uw-x/tinysdr/hardware/pcb-tinysdr/XSDR_FPGA_back.kicad_sch

## KiCad design hardware/pcb-tinysdr/XSDR_FPGA_back.kicad_sch (2022-02-07)

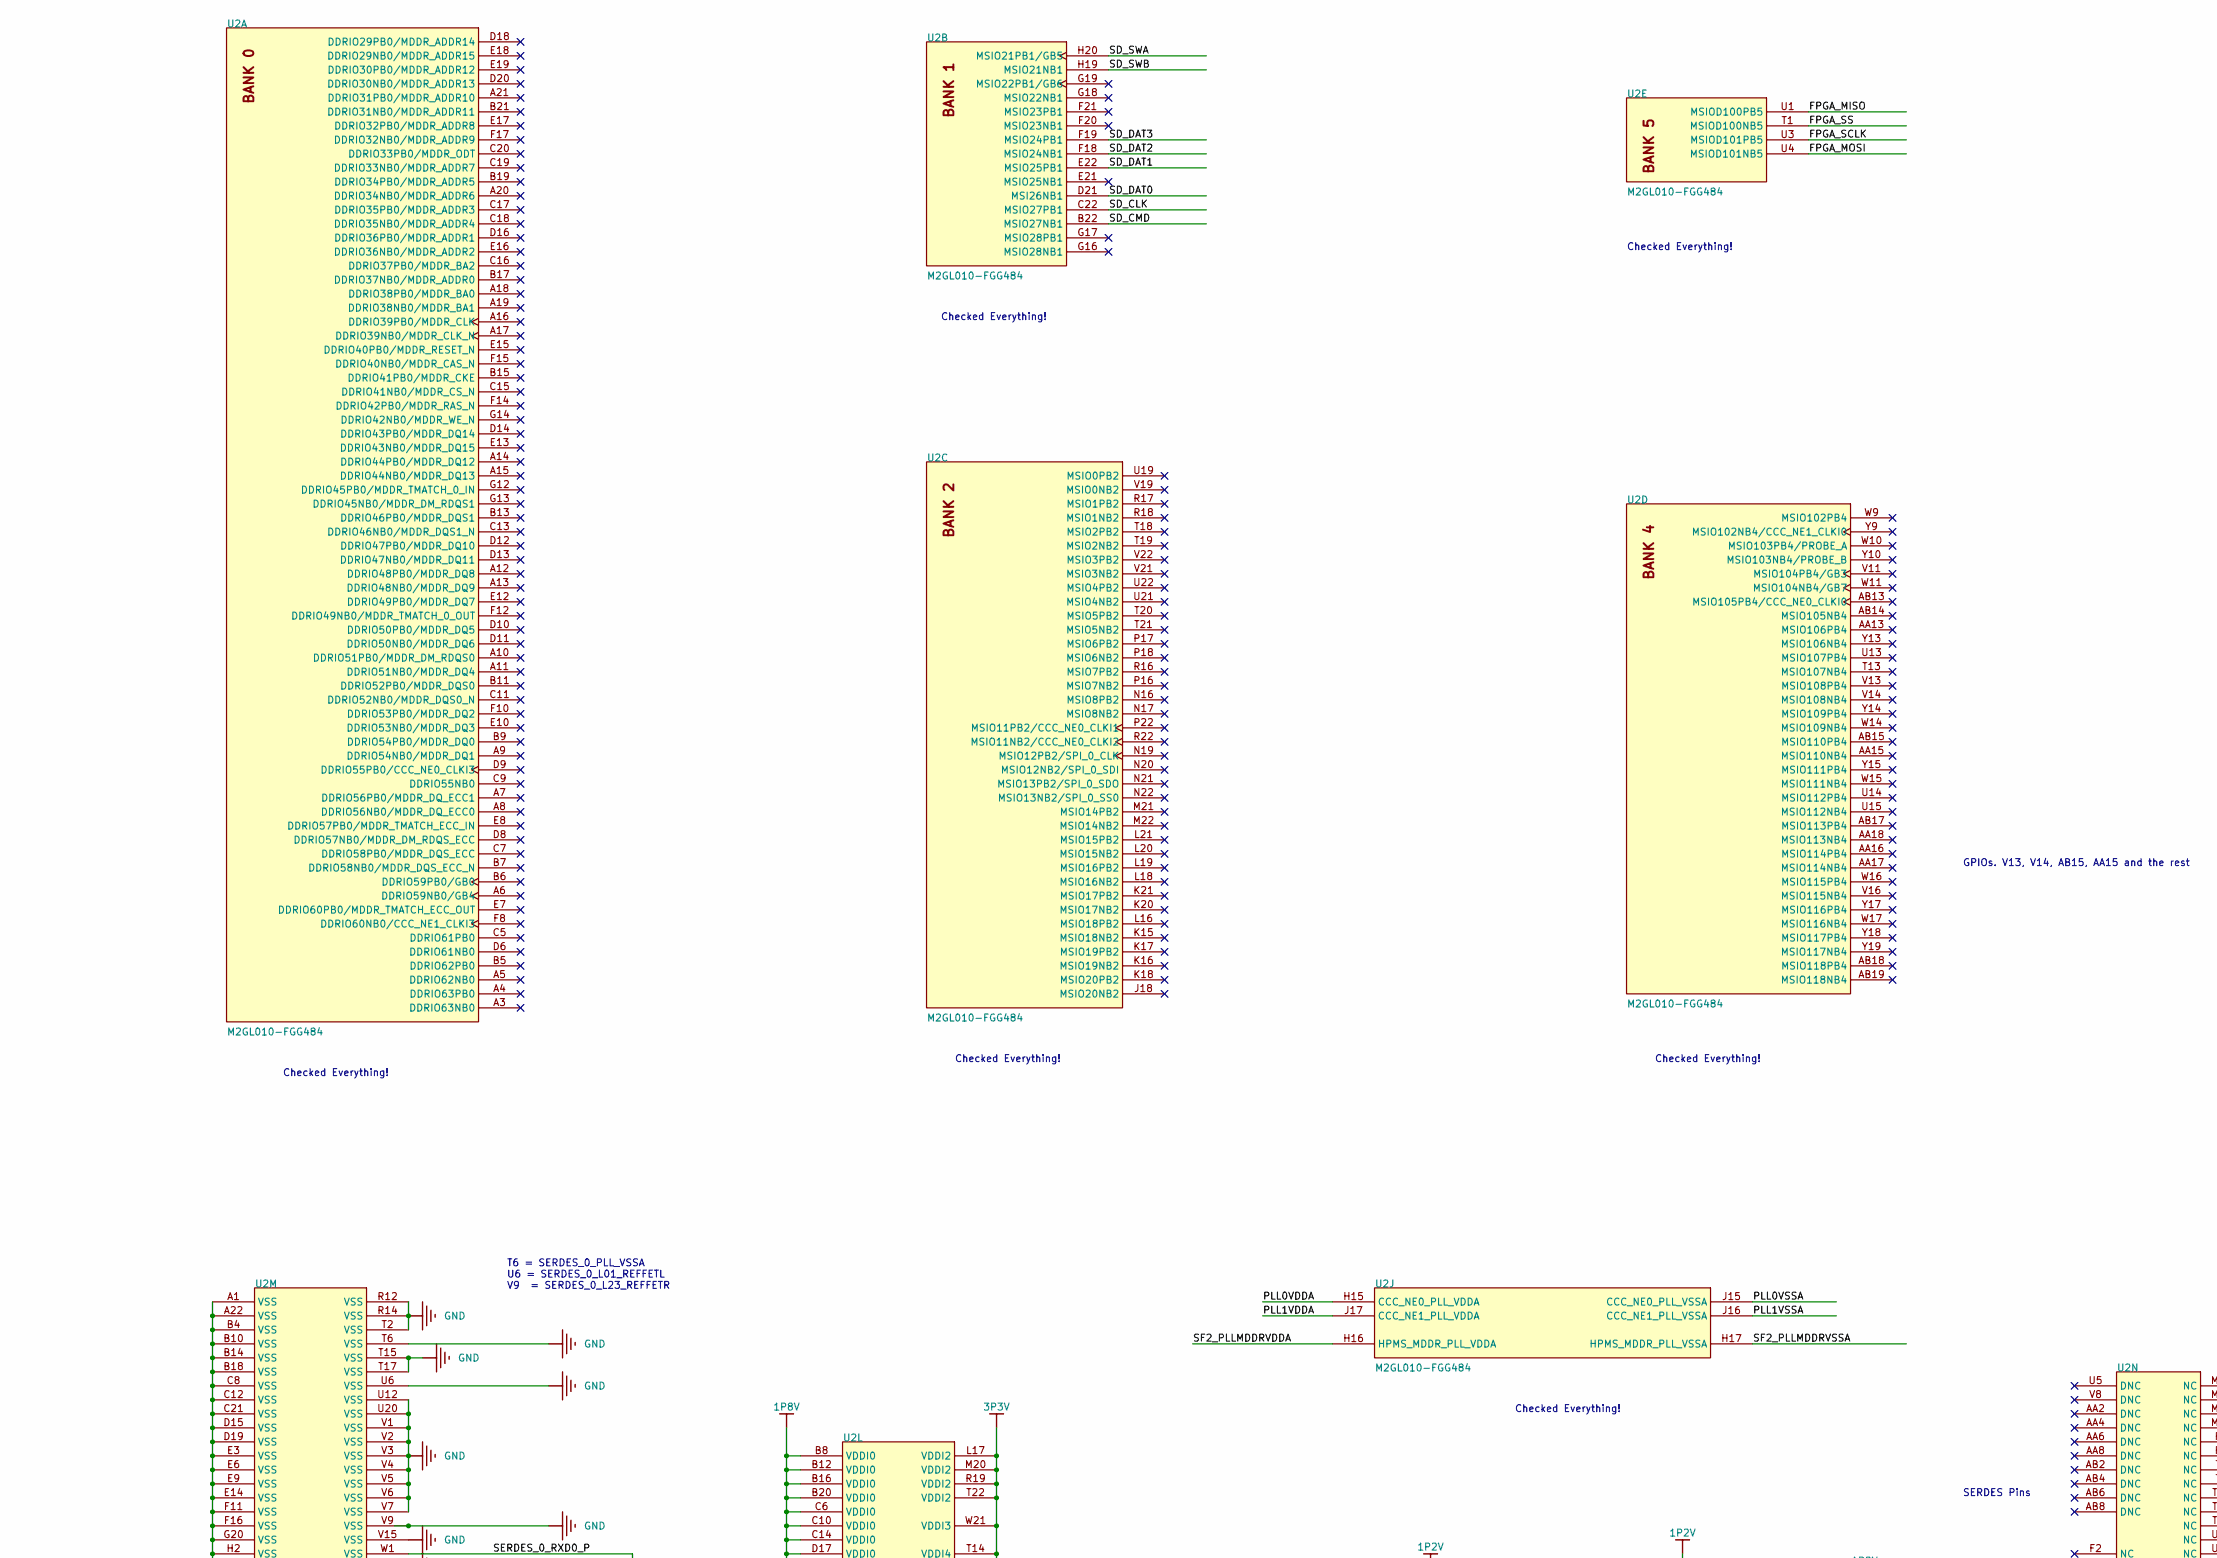
[picture p29: schematic XSDR_FPGA_back.kicad_sch, part in row 1, column 1]

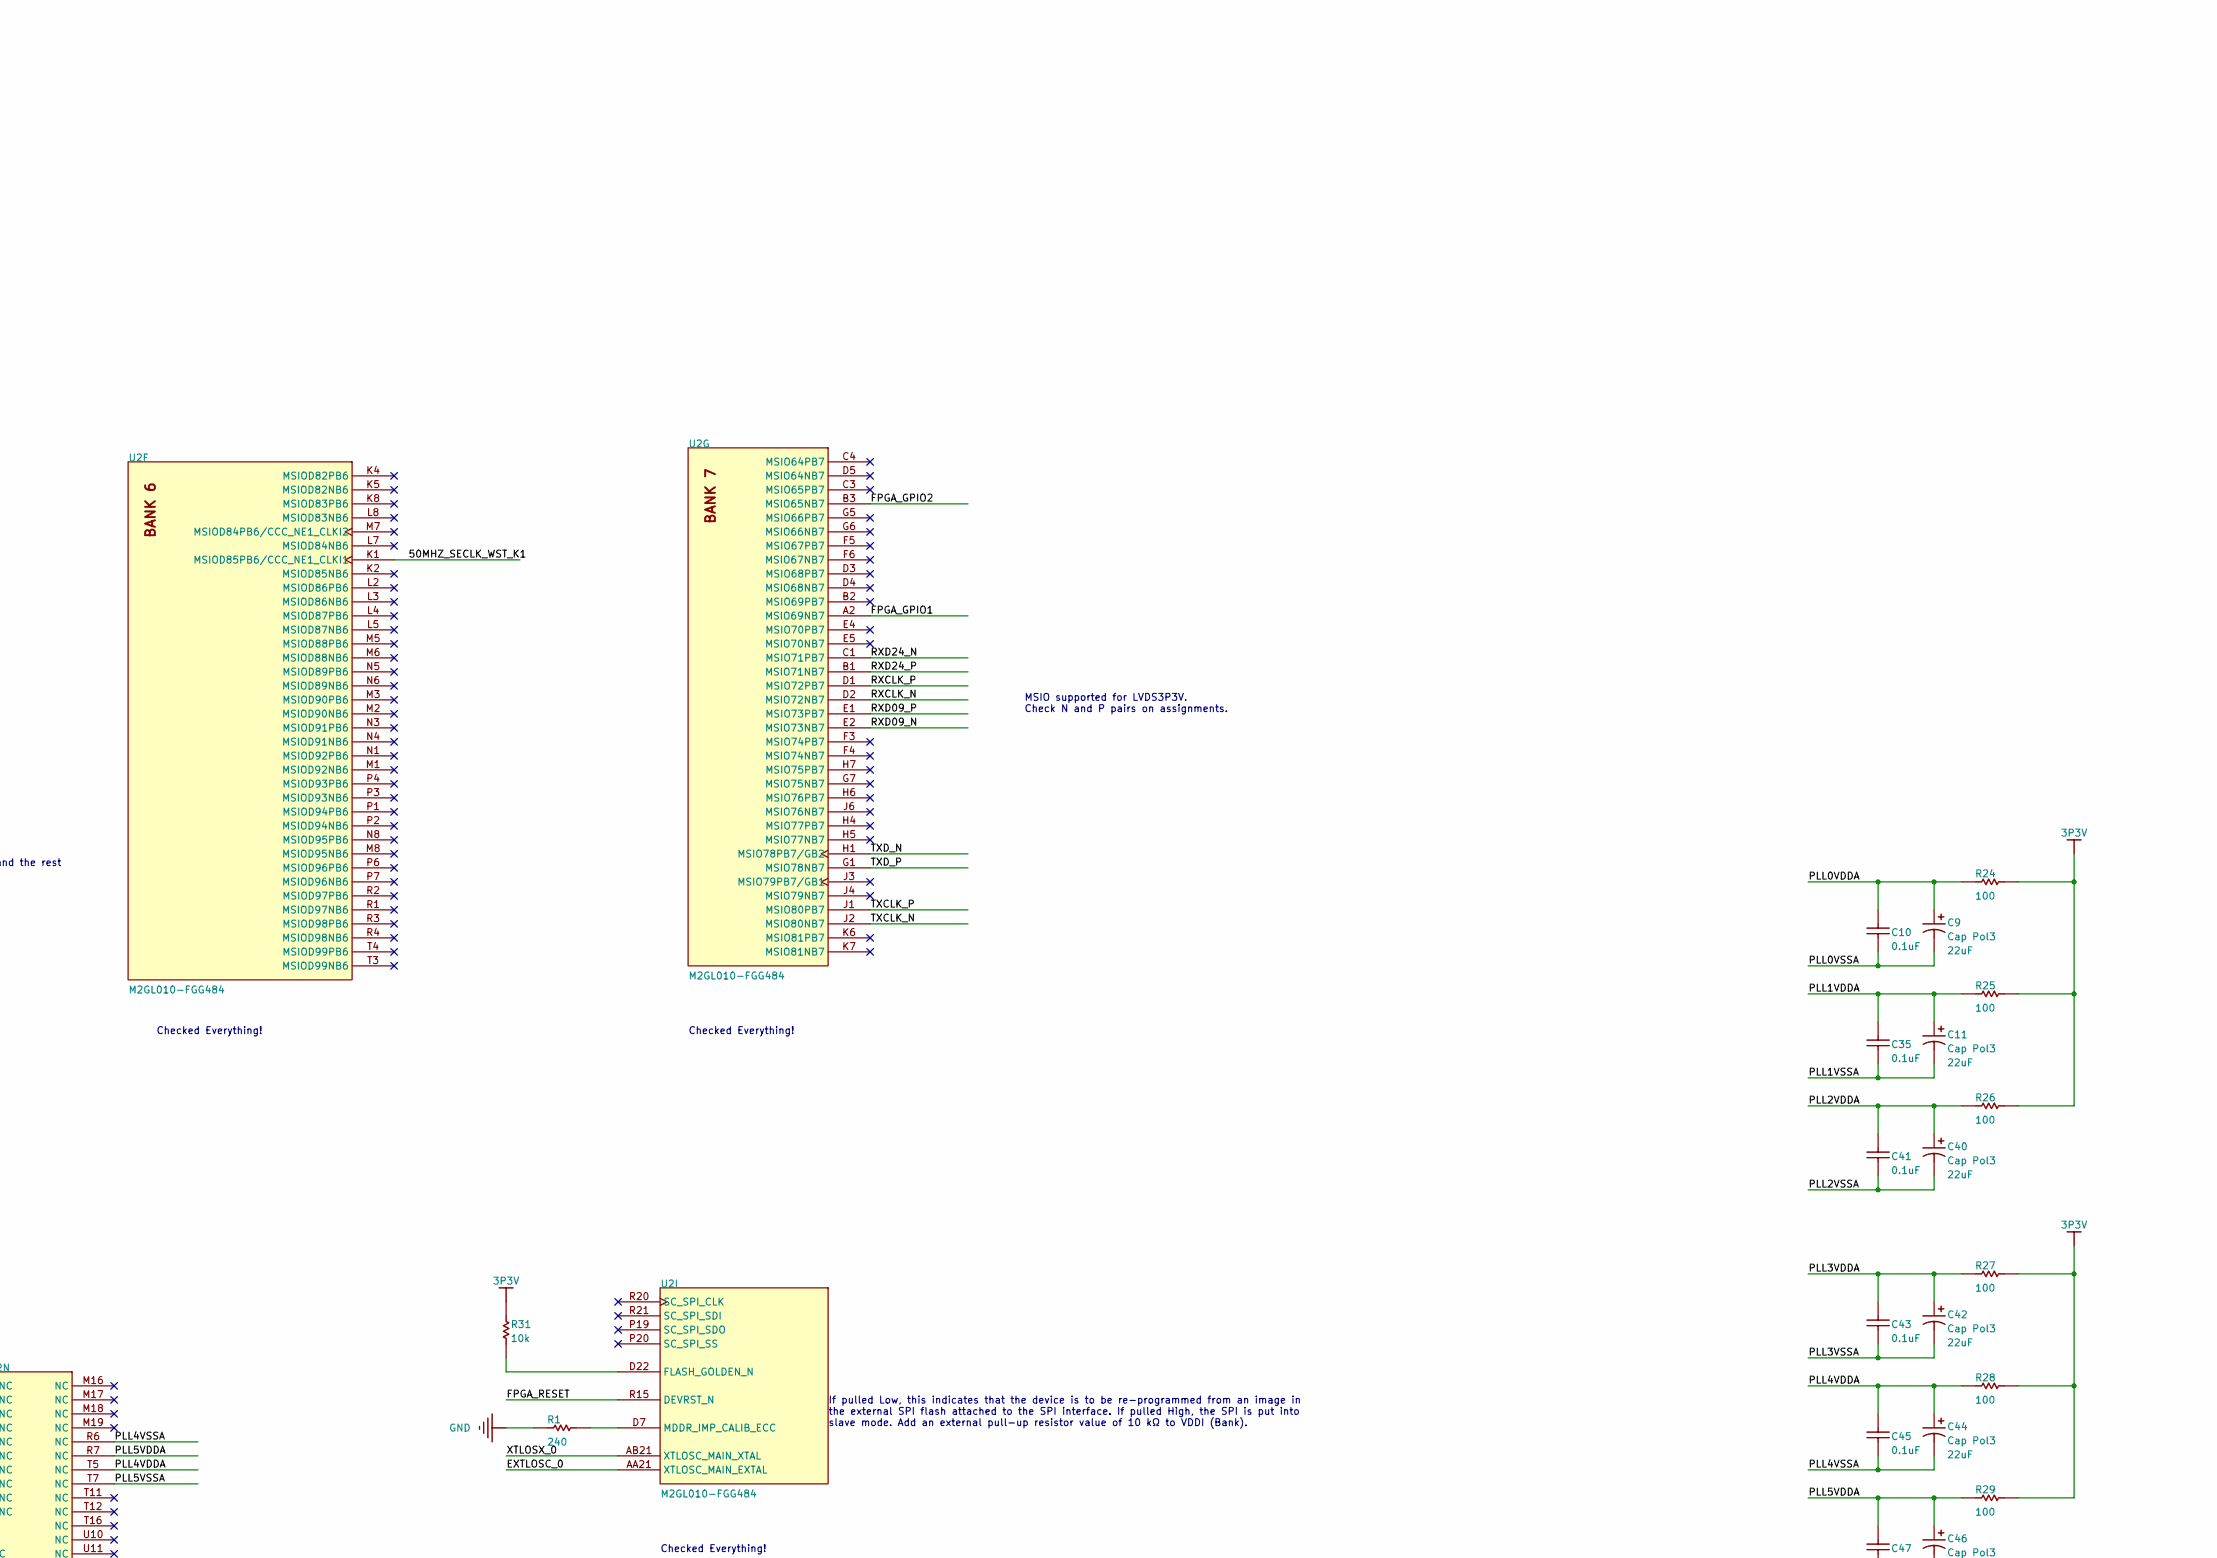
[picture p30: schematic XSDR_FPGA_back.kicad_sch, part in row 1, column 2]

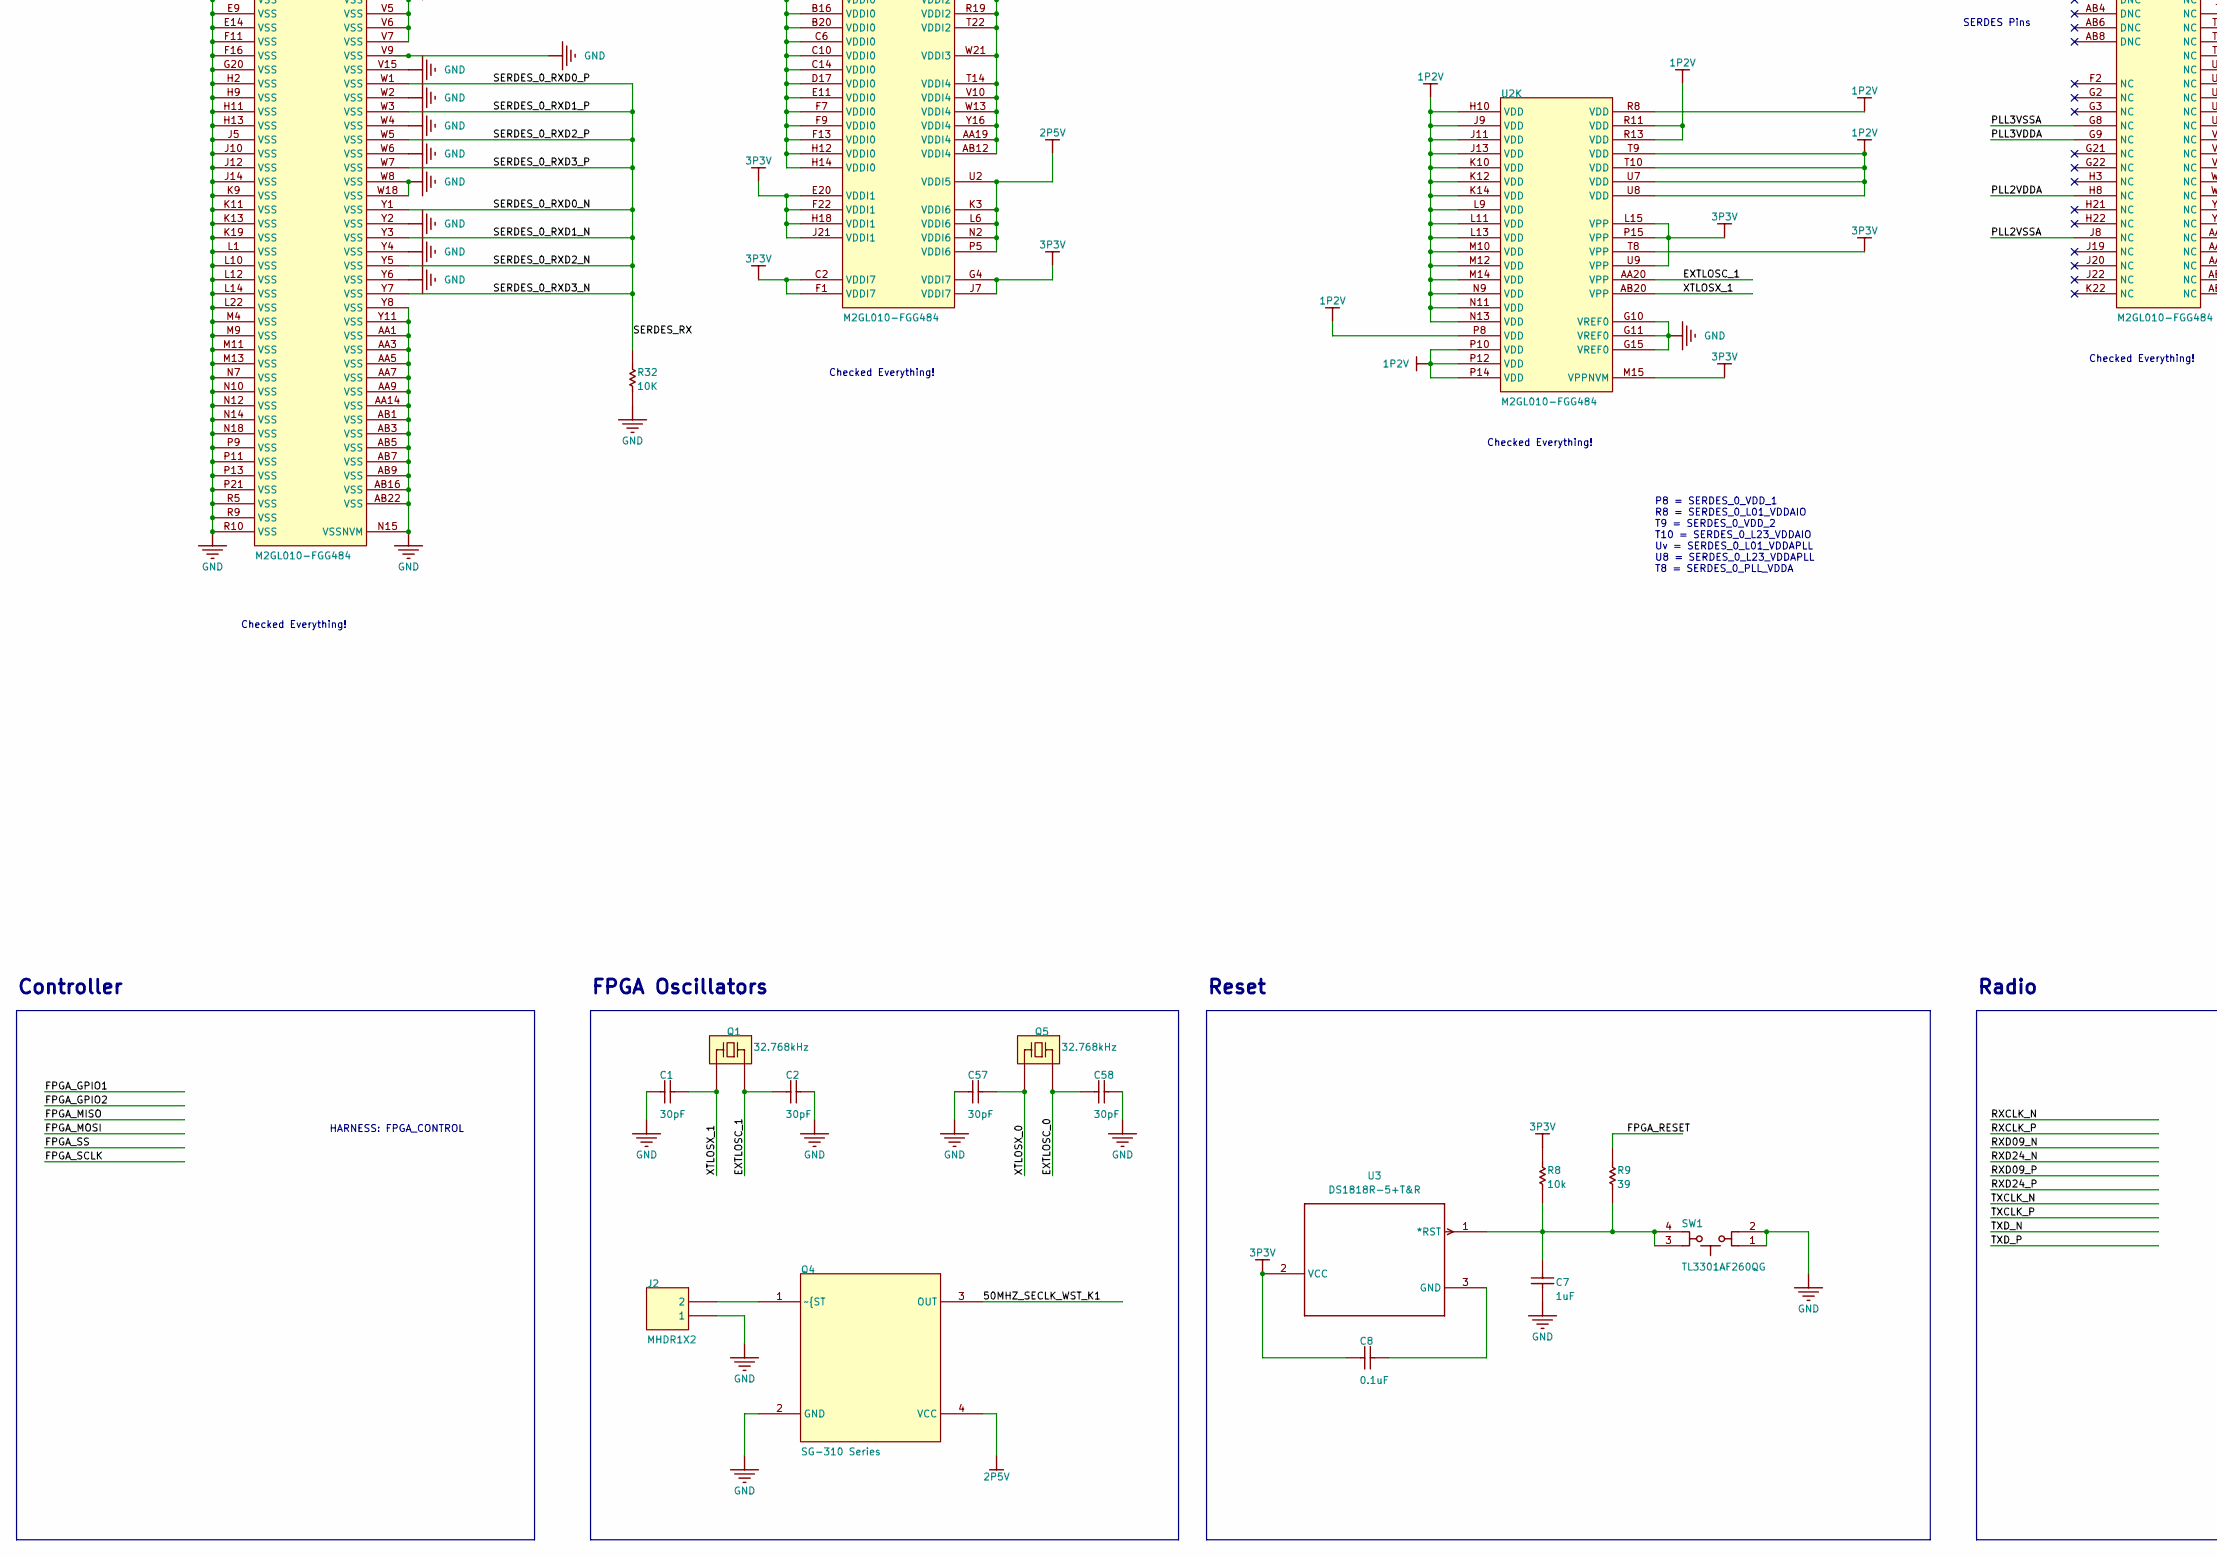
[picture p31: schematic XSDR_FPGA_back.kicad_sch, part in row 2, column 1]

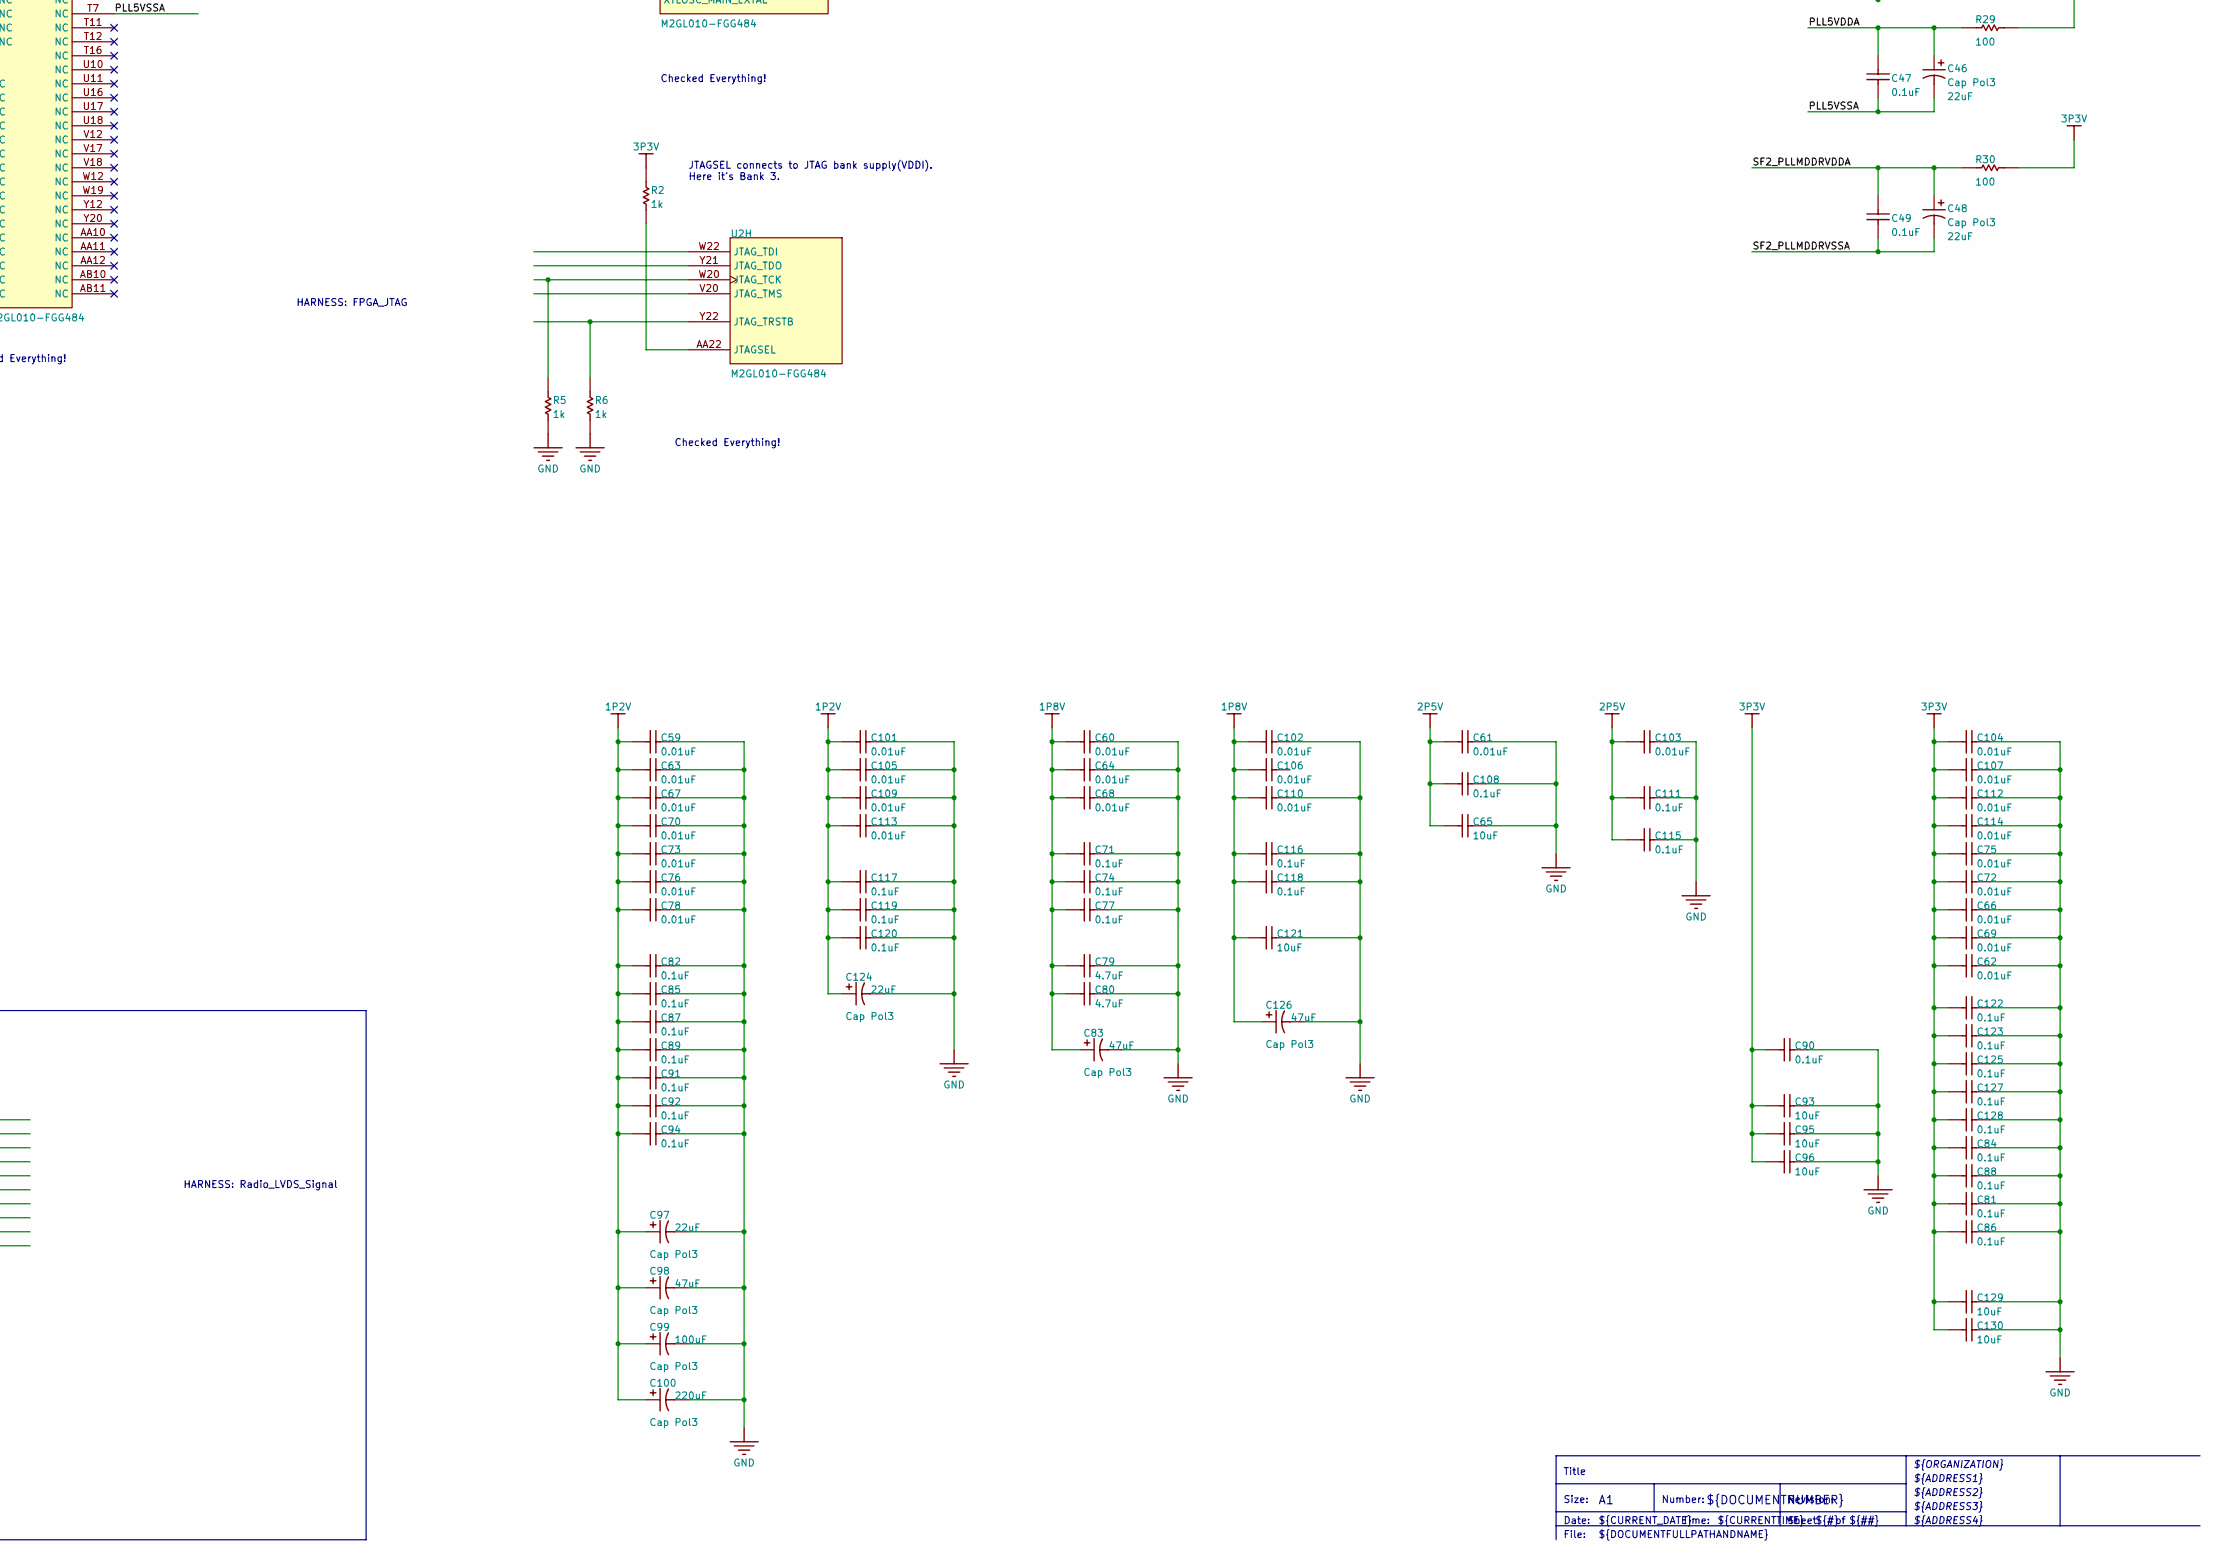
[picture p32: schematic XSDR_FPGA_back.kicad_sch, part in row 2, column 2]

Parts:
C1, C2, C57, C58: C_crystal; 0402; MPN GJM1555C1H300FB01D; DIGI-KEY PART NUMBER 490-16379-1-ND
C7: C_crystal; 0402; MPN CL05A105KL5NRNC; DIGI-KEY PART NUMBER 1276-6796-1-ND
C8, C81, C84, C86, C88, C90, C108, C111, C115, C116, C117, C118, C119, C120, C122, C123, C125, C127, C128: C_crystal; 0402; MPN GRM155R71A104KA01J; DIGI-KEY PART NUMBER 490-6322-1-ND
C9, C11, C40, C42, C44, C46, C48, C97, C124: Cap Pol3; C0805; MPN CL21A226MQCLQNC; DIGI-KEY PART NUMBER 1276-2412-1-ND
C10, C35, C41, C43, C45, C47, C49: Cap; 0402; RATING *; MPN GRM155R71A104KA01J; DIGI-KEY PART NUMBER 490-6322-1-ND
C59, C60, C63, C64, C67, C68, C70, C73, C76, C78: C_crystal; 0201; MPN GRM033R61E103KA12D; DIGI-KEY PART NUMBER 490-7194-1-ND
C61, C62, C66, C69, C72, C75, C101, C102, C103, C104, C105, C106, C107, C109, C110, C112, C113, C114: C_crystal; 0402; MPN GCM155R71H103KA55D; DIGI-KEY PART NUMBER 490-4762-1-ND
C65, C93, C95, C96, C121, C129, C130: C_crystal; 0402; MPN GRM155R60G106ME44D; DIGI-KEY PART NUMBER 490-10693-1-ND
C71, C74, C77, C82, C85, C87, C89, C91, C92, C94: C_crystal; 0201; MPN GRM033C71C104KE14D; DIGI-KEY PART NUMBER 490-10387-1-ND
C79, C80: C_crystal; 0201; MPN GRM035R60J475ME15D; DIGI-KEY PART NUMBER 490-13230-1-ND
C83, C98, C126: Cap Pol3; C0805; MPN GRM21BR60J476ME15L; DIGI-KEY PART NUMBER 490-9960-1-ND
C99: Cap Pol3; C0805; MPN GRM21BR60J107ME15L; DIGI-KEY PART NUMBER 490-13981-1-ND
C100: Cap Pol3; C0805; MPN 298D227X0004P2T; DIGI-KEY PART NUMBER 718-1894-1-ND
J2: MHDR1X2; MPN GRPB021VWVN-RC; DIGI-KEY PART NUMBER S9014E-02-ND
Q1, Q5: XTAL; XTAL [3.20mm x 1.50mm]; MPN FC-135 32.7680KA-A3; DIGI-KEY PART NUMBER SE2413CT-ND
Q4: SG-310 Series; SG-310SDN; MPN SG-310SDN 50.0000MJ3; DIGI-KEY PART NUMBER SER3714CT-ND
R1: Res; 0402; RATING *; MPN ERA-2AEB241X; DIGI-KEY PART NUMBER P240DCCT-ND
R2, R5, R6: Res; 0402; RATING *; MPN ERA-2AEB102X; DIGI-KEY PART NUMBER P1.0KDCCT-ND
R8, R31, R32: Res; 0402; RATING *; MPN ERA-2AEB103X; DIGI-KEY PART NUMBER P10KDCCT-ND
R9: Res; 0402; RATING *; MPN ERJ-2GEJ390X; DIGI-KEY PART NUMBER P39JCT-ND
R24, R25, R26, R27, R28, R29, R30: Res; 0402; RATING *; MPN ERA-2AED101X; DIGI-KEY PART NUMBER P100DECT-ND
SW1: TL3301AF260QG; ESWI-TL3301AF260QG_V; CONTACT RATING @ VOLTAGE 0.05A@12VDC; MPN TL3301AF260QG; DIGI-KEY PART NUMBER EG2527CT-ND
U2: M2GL010-FGG484; MCSM-FG-484; MPN M2GL010-FGG484; DIGI-KEY PART NUMBER 1100-1204-ND
U3: DS1818R-5+T&R; 21-0051H; MPN DS1818R-5+T&R; DIGI-KEY PART NUMBER DS1818R-5+CT-ND

Connections:
50MHZ_SECLK_WST_K1: Q4.3 (OUT), U2.K1 (MSIOD85PB6/CCC_NE1_CLKI1)
EXTLOSC_0: C58.1, Q5.1, U2.AA21 (XTLOSC_MAIN_EXTAL)
EXTLOSC_1: C2.1, Q1.1, U2.AA20 (VPP)
FPGA_GPIO1: U2.A2 (MSIO69NB7)
FPGA_GPIO2: U2.B3 (MSIO65NB7)
FPGA_MISO: U2.U1 (MSIOD100PB5)
FPGA_MOSI: U2.U4 (MSIOD101NB5)
FPGA_RESET: R9.1, U2.R15 (DEVRST_N)
FPGA_SCLK: U2.U3 (MSIOD101PB5)
FPGA_SS: U2.T1 (MSIOD100NB5)
unnamed: C7.2, R8.2, R9.2, SW1.3, SW1.4, U3.1 (*RST)
unnamed: C8.1, U3.2 (VCC)
unnamed: C8.2, U3.3 (GND)
unnamed: C60.1, C64.1, C68.1, C71.1, C74.1, C77.1, C79.1, C80.1, C83.2
unnamed: C60.2, C64.2, C68.2, C71.2, C74.2, C77.2, C79.2, C80.2, C83.1
unnamed: C90.1, C93.1, C95.1, C96.1
unnamed: C90.2, C93.2, C95.2, C96.2
unnamed: C59.2, C63.2, C67.2, C70.2, C73.2, C76.2, C78.2, C82.2, C85.2, C87.2, C89.2, C91.2, C92.2, C94.2, C97.1, C98.1, C99.1, C100.1
unnamed: C59.1, C63.1, C67.1, C70.1, C73.1, C76.1, C78.1, C82.1, C85.1, C87.1, C89.1, C91.1, C92.1, C94.1, C97.2, C98.2, C99.2, C100.2
unnamed: C101.1, C105.1, C109.1, C113.1, C117.1, C119.1, C120.1, C124.2
unnamed: C101.2, C105.2, C109.2, C113.2, C117.2, C119.2, C120.2, C124.1
unnamed: C102.1, C110.1, C116.1, C118.1, C121.1, C126.2
unnamed: C102.2, C106.2, C110.2, C116.2, C118.2, C121.2, C126.1
unnamed: C103.1, C111.1, C115.1
unnamed: C103.2, C111.2, C115.2
unnamed: C62.1, C66.1, C69.1, C72.1, C75.1, C81.1, C84.1, C86.1, C88.1, C104.1, C107.1, C112.1, C114.1, C122.1, C123.1, C125.1, C127.1, C128.1, C129.1, C130.1
unnamed: C62.2, C66.2, C69.2, C72.2, C75.2, C81.2, C84.2, C86.2, C88.2, C104.2, C107.2, C112.2, C114.2, C122.2, C123.2, C125.2, C127.2, C128.2, C129.2, C130.2
unnamed: C61.1, C65.1, C108.1
unnamed: C61.2, C65.2, C108.2
unnamed: J2.2, Q4.1 (~{ST)
unnamed: R1.2, U2.D7 (MDDR_IMP_CALIB_ECC)
unnamed: R2.1, U2.AA22 (JTAGSEL)
unnamed: R5.2, U2.W20 (JTAG_TCK)
unnamed: R6.2, U2.Y22 (JTAG_TRSTB)
unnamed: R24.2, R25.2, R26.2
unnamed: R27.2, R28.2, R29.2
unnamed: R31.1, U2.D22 (FLASH_GOLDEN_N)
unnamed: SW1.1, SW1.2
unnamed: U2.A1 (VSS), U2.A22 (VSS), U2.B4 (VSS), U2.B10 (VSS), U2.B14 (VSS), U2.B18 (VSS), U2.C8 (VSS), U2.C12 (VSS), U2.C21 (VSS), U2.D15 (VSS), U2.D19 (VSS), U2.E3 (VSS), U2.E6 (VSS), U2.E9 (VSS), U2.E14 (VSS), U2.F11 (VSS), U2.F16 (VSS), U2.G20 (VSS), U2.H2 (VSS), U2.H9 (VSS), U2.H11 (VSS), U2.H13 (VSS), U2.J5 (VSS), U2.J10 (VSS), U2.J12 (VSS), U2.J14 (VSS), U2.K9 (VSS), U2.K11 (VSS), U2.K13 (VSS), U2.K19 (VSS), U2.L1 (VSS), U2.L10 (VSS), U2.L12 (VSS), U2.L14 (VSS), U2.L22 (VSS), U2.M4 (VSS), U2.M9 (VSS), U2.M11 (VSS), U2.M13 (VSS), U2.N7 (VSS), U2.N10 (VSS), U2.N12 (VSS), U2.N14 (VSS), U2.N18 (VSS), U2.P9 (VSS), U2.P11 (VSS), U2.P13 (VSS), U2.P21 (VSS), U2.R5 (VSS), U2.R9 (VSS), U2.R10 (VSS)
unnamed: U2.AA1 (VSS), U2.AA3 (VSS), U2.AA5 (VSS), U2.AA7 (VSS), U2.AA9 (VSS), U2.AA14 (VSS), U2.AB1 (VSS), U2.AB3 (VSS), U2.AB5 (VSS), U2.AB7 (VSS), U2.AB9 (VSS), U2.AB16 (VSS), U2.AB22 (VSS), U2.N15 (VSSNVM), U2.Y8 (VSS), U2.Y11 (VSS)
unnamed: U2.AA19 (VDDI4), U2.AB12 (VDDI4), U2.L17 (VDDI2), U2.M20 (VDDI2), U2.R19 (VDDI2), U2.T14 (VDDI4), U2.T22 (VDDI2), U2.V10 (VDDI4), U2.W13 (VDDI4), U2.W21 (VDDI3), U2.Y16 (VDDI4)
unnamed: U2.B8 (VDDI0), U2.B12 (VDDI0), U2.B16 (VDDI0), U2.B20 (VDDI0), U2.C6 (VDDI0), U2.C10 (VDDI0), U2.C14 (VDDI0), U2.D17 (VDDI0), U2.E11 (VDDI0), U2.F7 (VDDI0), U2.F9 (VDDI0), U2.F13 (VDDI0), U2.H12 (VDDI0), U2.H14 (VDDI0)
unnamed: U2.C2 (VDDI7), U2.F1 (VDDI7)
unnamed: U2.E20 (VDDI1), U2.F22 (VDDI1), U2.H18 (VDDI1), U2.J21 (VDDI1)
unnamed: U2.G4 (VDDI7), U2.J7 (VDDI7)
unnamed: U2.G10 (VREF0), U2.G11 (VREF0), U2.G15 (VREF0)
unnamed: U2.H10 (VDD), U2.J9 (VDD), U2.J11 (VDD), U2.J13 (VDD), U2.K10 (VDD), U2.K12 (VDD), U2.K14 (VDD), U2.L9 (VDD), U2.L11 (VDD), U2.L13 (VDD), U2.M10 (VDD), U2.M12 (VDD), U2.M14 (VDD), U2.N9 (VDD), U2.N11 (VDD), U2.N13 (VDD)
unnamed: U2.K3 (VDDI6), U2.L6 (VDDI6), U2.N2 (VDDI6), U2.P5 (VDDI6), U2.U2 (VDDI5)
unnamed: U2.L15 (VPP), U2.P15 (VPP), U2.U9 (VPP)
unnamed: U2.P10 (VDD), U2.P12 (VDD), U2.P14 (VDD)
unnamed: U2.R11 (VDD), U2.R13 (VDD)
unnamed: U2.R12 (VSS), U2.R14 (VSS), U2.T2 (VSS)
unnamed: U2.T9 (VDD), U2.T10 (VDD), U2.U7 (VDD), U2.U8 (VDD)
unnamed: U2.T15 (VSS), U2.T17 (VSS)
unnamed: U2.U12 (VSS), U2.U20 (VSS), U2.V1 (VSS), U2.V2 (VSS), U2.V3 (VSS), U2.V4 (VSS), U2.V5 (VSS), U2.V6 (VSS), U2.V7 (VSS)
unnamed: U2.W8 (VSS), U2.W18 (VSS)
PLL0VDDA: C9.1, C10.2, R24.1, U2.H15 (CCC_NE0_PLL_VDDA)
PLL0VSSA: C9.2, C10.1, U2.J15 (CCC_NE0_PLL_VSSA)
PLL1VDDA: C11.1, C35.2, R25.1, U2.J17 (CCC_NE1_PLL_VDDA)
PLL1VSSA: C11.2, C35.1, U2.J16 (CCC_NE1_PLL_VSSA)
PLL2VDDA: C40.1, C41.2, R26.1, U2.H8 (NC)
PLL2VSSA: C40.2, C41.1, U2.J8 (NC)
PLL3VDDA: C42.1, C43.2, R27.1, U2.G9 (NC)
PLL3VSSA: C42.2, C43.1, U2.G8 (NC)
PLL4VDDA: C44.1, C45.2, R28.1, U2.T5 (NC)
PLL4VSSA: C44.2, C45.1, U2.R6 (NC)
PLL5VDDA: C46.1, C47.2, R29.1, U2.R7 (NC)
PLL5VSSA: C46.2, C47.1, U2.T7 (NC)
RXCLK_N: U2.D2 (MSIO72NB7)
RXCLK_P: U2.D1 (MSIO72PB7)
RXD09_N: U2.E2 (MSIO73NB7)
RXD09_P: U2.E1 (MSIO73PB7)
RXD24_N: U2.C1 (MSIO71PB7)
RXD24_P: U2.B1 (MSIO71NB7)
SD_CLK: U2.C22 (MSIO27PB1)
SD_CMD: U2.B22 (MSIO27NB1)
SD_DAT0: U2.D21 (MSI26NB1)
SD_DAT1: U2.E22 (MSIO25PB1)
SD_DAT2: U2.F18 (MSIO24NB1)
SD_DAT3: U2.F19 (MSIO24PB1)
SD_SWA: U2.H20 (MSIO21PB1/GB5)
SD_SWB: U2.H19 (MSIO21NB1)
SERDES_0_RXD0_N: R32.2, U2.W1 (VSS), U2.W3 (VSS), U2.W5 (VSS), U2.W7 (VSS), U2.Y1 (VSS), U2.Y3 (VSS), U2.Y5 (VSS), U2.Y7 (VSS)
SF2_PLLMDDRVDDA: C48.1, C49.2, R30.1, U2.H16 (HPMS_MDDR_PLL_VDDA)
SF2_PLLMDDRVSSA: C48.2, C49.1, U2.H17 (HPMS_MDDR_PLL_VSSA)
TXCLK_N: U2.J2 (MSIO80NB7)
TXCLK_P: U2.J1 (MSIO80PB7)
TXD_N: U2.H1 (MSIO78PB7/GB2)
TXD_P: U2.G1 (MSIO78NB7)
XTLOSX_0: C57.2, Q5.2, U2.AB21 (XTLOSC_MAIN_XTAL)
XTLOSX_1: C1.2, Q1.2, U2.AB20 (VPP)

Notes on the sheet:
${REVISION}
Checked Everything!
${TITLE}
${DOCUMENTFULLPATHANDNAME}
${##}
Number:
${ADDRESS3}
Controller
HARNESS: Radio_LVDS_Signal
SERDES Pins
Date:
HARNESS: FPGA_JTAG
Radio
${ADDRESS4}
${ADDRESS1}
JTAGSEL connects to JTAG bank supply(VDDI). Here it's Bank 3.
${DOCUMENTNUMBER}
Time:
MSIO supported for LVDS3P3V. Check N and P pairs on assignments.
${CURRENTTIME}
Sheet
P8 = SERDES_0_VDD_1 R8 = SERDES_0_L01_VDDAIO T9 = SERDES_0_VDD_2 T10 = SERDES_0_L23_VDDAIO Uv = SERDES_0_L01_VDDAPLL U8 = SERDES_0_L23_VDDAPLL T8 = SERDES_0_PLL_VDDA
${#}
Title
${CURRENT_DATE}
T6 = SERDES_0_PLL_VSSA U6 = SERDES_0_L01_REFFETL V9 = SERDES_0_L23_REFFETR
Reset
FPGA Oscillators
Size:
File:
HARNESS: FPGA_CONTROL
${ORGANIZATION}
If pulled Low, this indicates that the device is to be re-programmed from an image in the external SPI flash attached to the SPI interface. If pulled High, the SPI is put into slave mode. Add an external pull-up resistor value of 10 kΩ to VDDI (Bank).
${ADDRESS2}
Revision:
GPIOs. V13, V14, AB15, AA15 and the rest
Checked Everything!
