uw-x/tinysdr/hardware/pcb-tinysdr/tinysdr_Backbone.kicad_sch

## KiCad design hardware/pcb-tinysdr/tinysdr_Backbone.kicad_sch (2022-02-07)

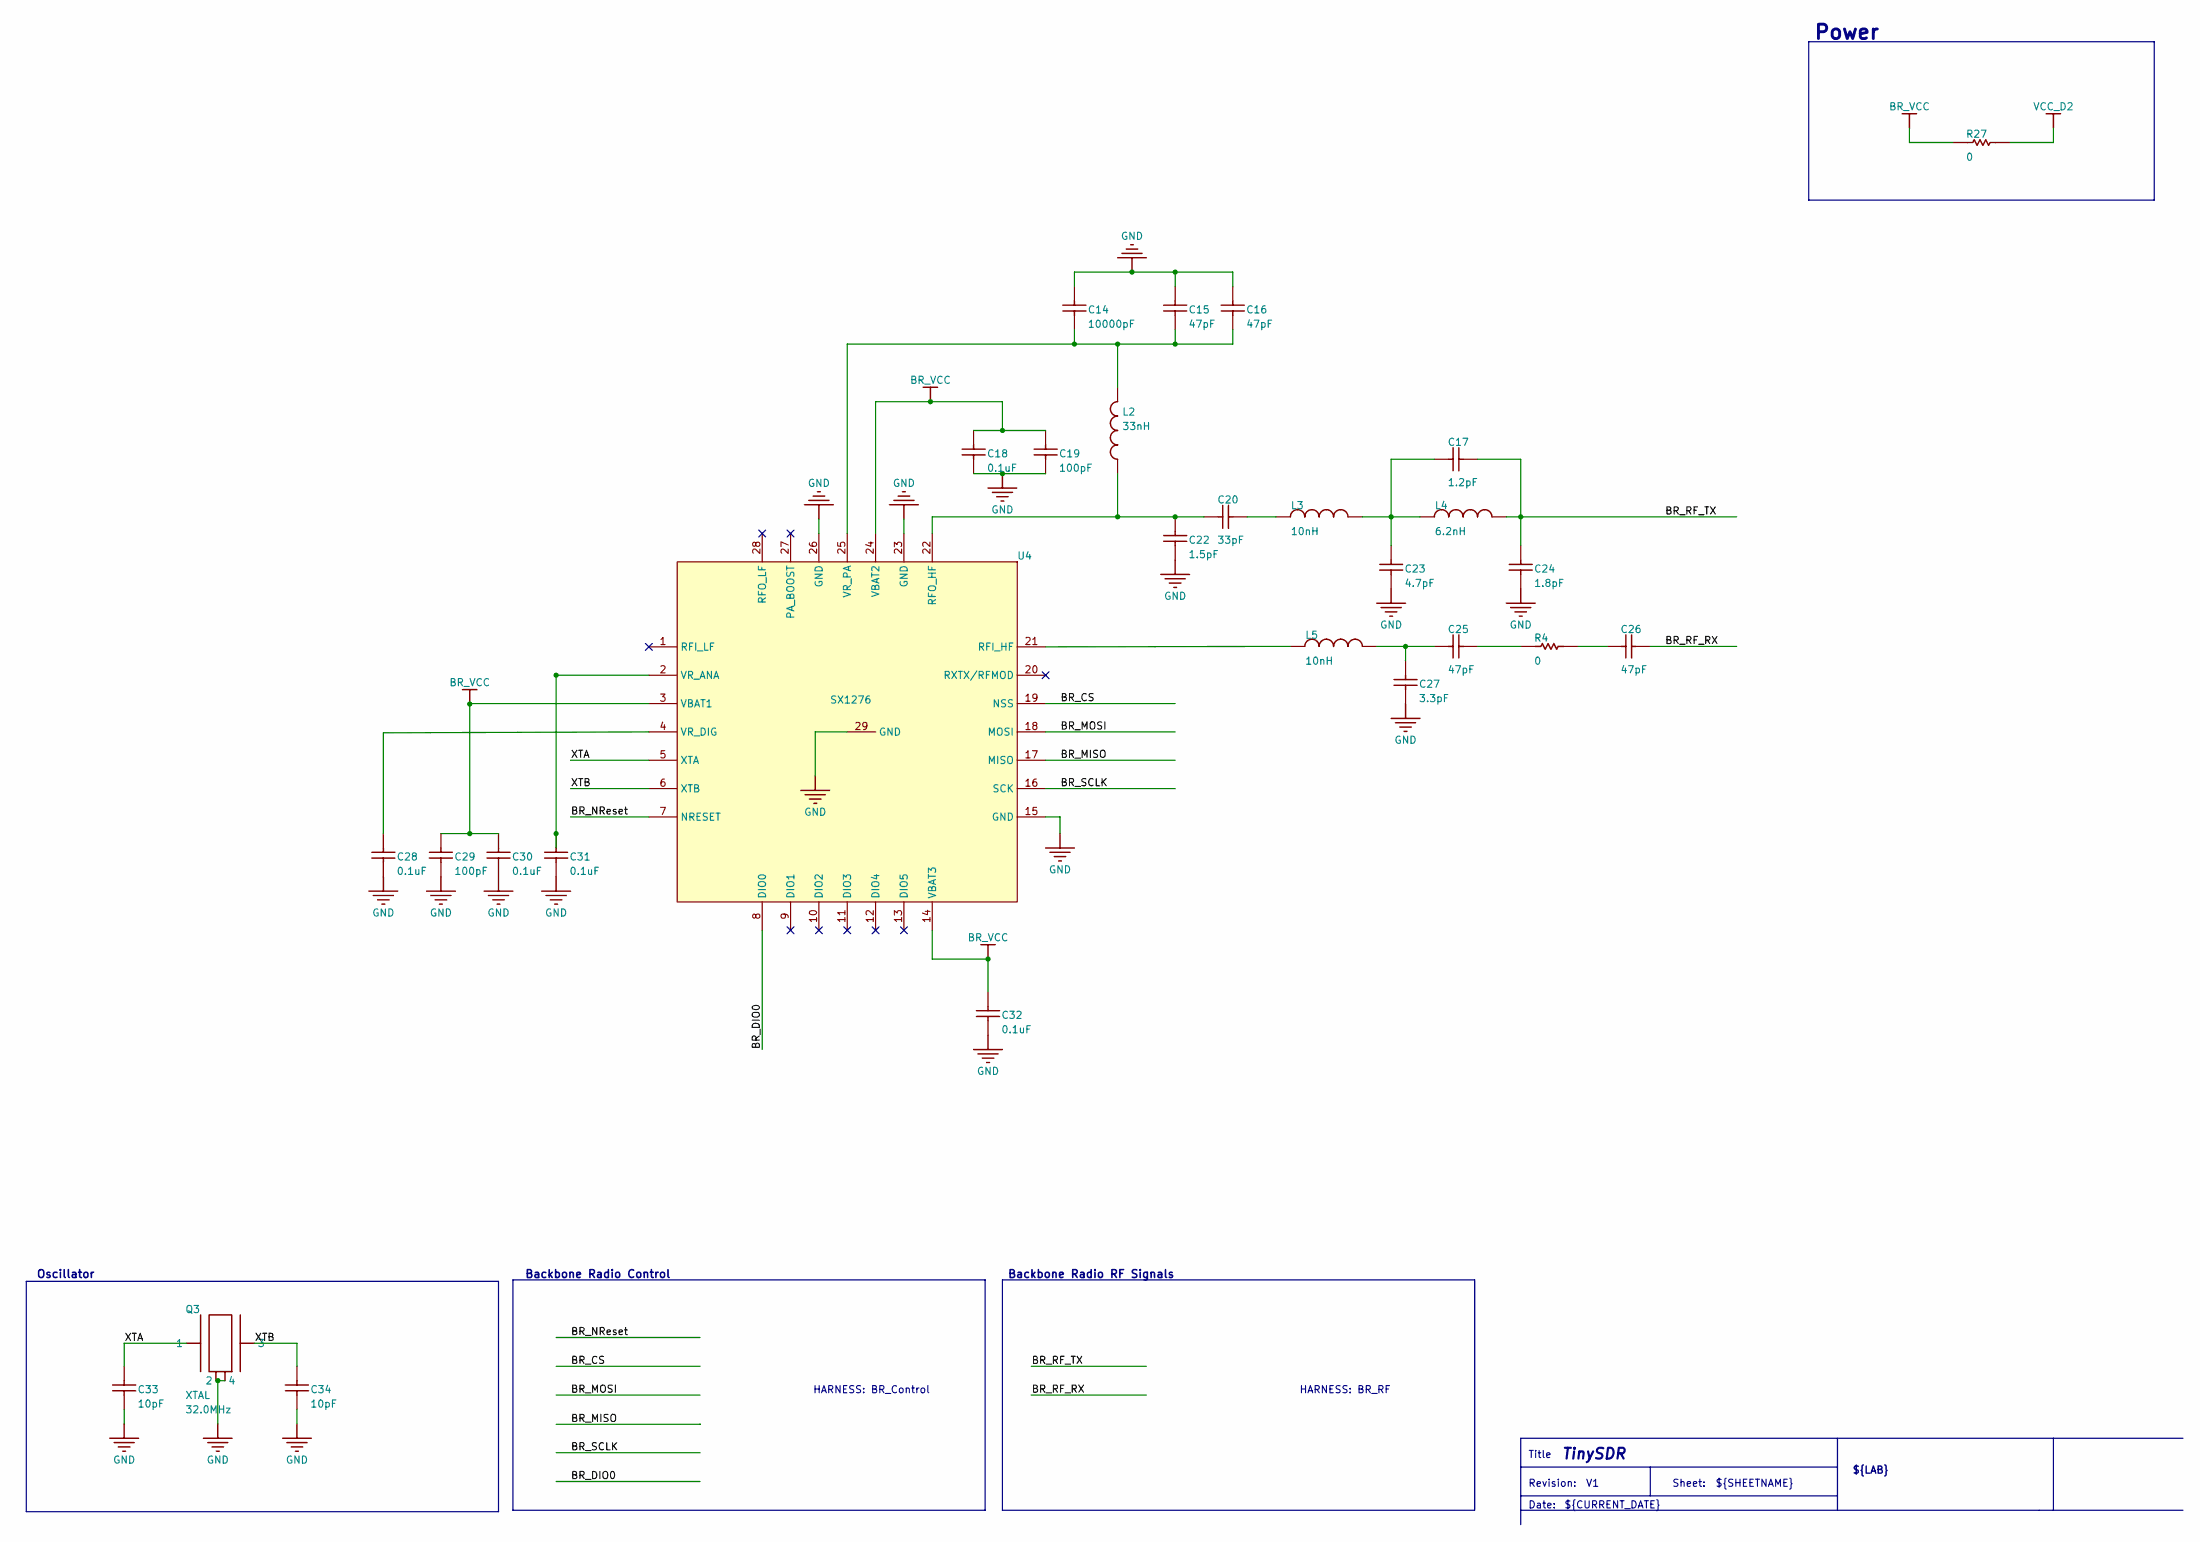
[picture p33: schematic tinysdr_Backbone.kicad_sch]

Parts:
C14: Cap; 0201; RATING *; MPN GRM033R61E103KA12D; DIGI-KEY PART NUMBER 490-7194-1-ND
C15, C16, C25, C26: Cap; 0201; RATING *; MPN GRM0335C1E470JA01J; DIGI-KEY PART NUMBER 490-14548-1-ND
C17: Cap; 0201; RATING *; MPN GRM0335C1H1R2CA01D; DIGI-KEY PART NUMBER 490-6119-1-ND
C18, C28, C30, C31, C32: Cap; 0201; RATING *; MPN GRM033C71C104KE14D; DIGI-KEY PART NUMBER 490-10387-1-ND
C19, C29: Cap; 0201; RATING *; MPN GRM0335C1H101JA01D; DIGI-KEY PART NUMBER 490-6113-1-ND
C20: Cap; 0201; RATING *; MPN GRM0335C1H330JA01D; DIGI-KEY PART NUMBER 490-6126-1-ND
C22: Cap; 0201; RATING *; MPN GRM0335C1E1R5CA01D; DIGI-KEY PART NUMBER 490-11287-1-ND
C23: Cap; 0201; RATING *; MPN GRM0335C1H4R7CA01D; DIGI-KEY PART NUMBER 490-6130-1-ND
C24: Cap; 0201; RATING *; MPN GRM0335C1H1R8CA01D; DIGI-KEY PART NUMBER 490-11314-1-ND
C27: Cap; 0201; RATING *; MPN GRM0335C1H3R3CA01D; DIGI-KEY PART NUMBER 490-6128-1-ND
C33, C34: Cap; 0201; RATING *; MPN GRM0335C1H100JA01D; DIGI-KEY PART NUMBER 490-6112-1-ND
L2: Ind; _work_pcb_xsdr_v2_Libraries_WREL_AD10_Ben.PcbLib_0201; RATING *; MANUFACTURER PART NUMBER *; DIGI-KEY PART NUMBER 490-6726-1-ND
L3, L5: Ind; _work_pcb_xsdr_v2_Libraries_WREL_AD10_Ben.PcbLib_0201; RATING *; MANUFACTURER PART NUMBER *; DIGI-KEY PART NUMBER 490-5568-1-ND
L4: Ind; _work_pcb_xsdr_v2_Libraries_WREL_AD10_Ben.PcbLib_0201; RATING *; MANUFACTURER PART NUMBER *; DIGI-KEY PART NUMBER 490-5563-1-ND
Q3: XTAL; nd2520da; MPN FL3200038Z; DIGI-KEY PART NUMBER FL3200038ZCT-ND
R4: Res; 0201; RATING *; MANUFACTURER PART NUMBER *; DIGI-KEY PART NUMBER P15979CT-ND
R27: Res; 0402; RATING *; MANUFACTURER PART NUMBER *; DIGI-KEY PART NUMBER 541-0.0YBCT-ND
U4: SX1276; vqfn28_6x6mm; MPN SX1276IMLTRT; DIGI-KEY PART NUMBER SX1276IMLTRTCT-ND

Connections:
BR_DIO0: U4.8 (DIO0)
BR_NReset: U4.7 (NRESET)
BR_RF_RX: C26.1
BR_RF_TX: C17.1, C24.2, L4.2
unnamed: C14.1, C15.1, C16.1
unnamed: C14.2, C15.2, C16.2, L2.2, U4.25 (VR_PA)
unnamed: C17.2, C23.1, L3.2, L4.1
unnamed: C18.1, C19.1
unnamed: C18.2, C19.2, U4.24 (VBAT2)
unnamed: C20.1, L3.1
unnamed: C20.2, C22.2, L2.1, U4.22 (RFO_HF)
unnamed: C25.1, R4.2
unnamed: C25.2, C27.2, L5.2
unnamed: C26.2, R4.1
unnamed: C28.2, U4.4 (VR_DIG)
unnamed: C29.2, C30.2, U4.3 (VBAT1)
unnamed: C31.2, U4.2 (VR_ANA)
unnamed: C32.2, U4.14 (VBAT3)
unnamed: Q3.2, Q3.4
XTA: C33.1, Q3.1, U4.5 (XTA)
XTB: C34.1, Q3.3, U4.6 (XTB)

Notes on the sheet:
HARNESS: BR_Control
${CURRENT_DATE}
HARNESS: BR_RF
Sheet:
${SHEETNAME}
Oscillator
Backbone Radio RF Signals
${TITLE}
Power
Date:
${REVISION}
Backbone Radio Control
Revision:
Title
${LAB}
