uw-x/tinysdr/hardware/pcb-tinysdr/tinysdr_Connectors.kicad_sch

## KiCad design hardware/pcb-tinysdr/tinysdr_Connectors.kicad_sch (2022-02-07)

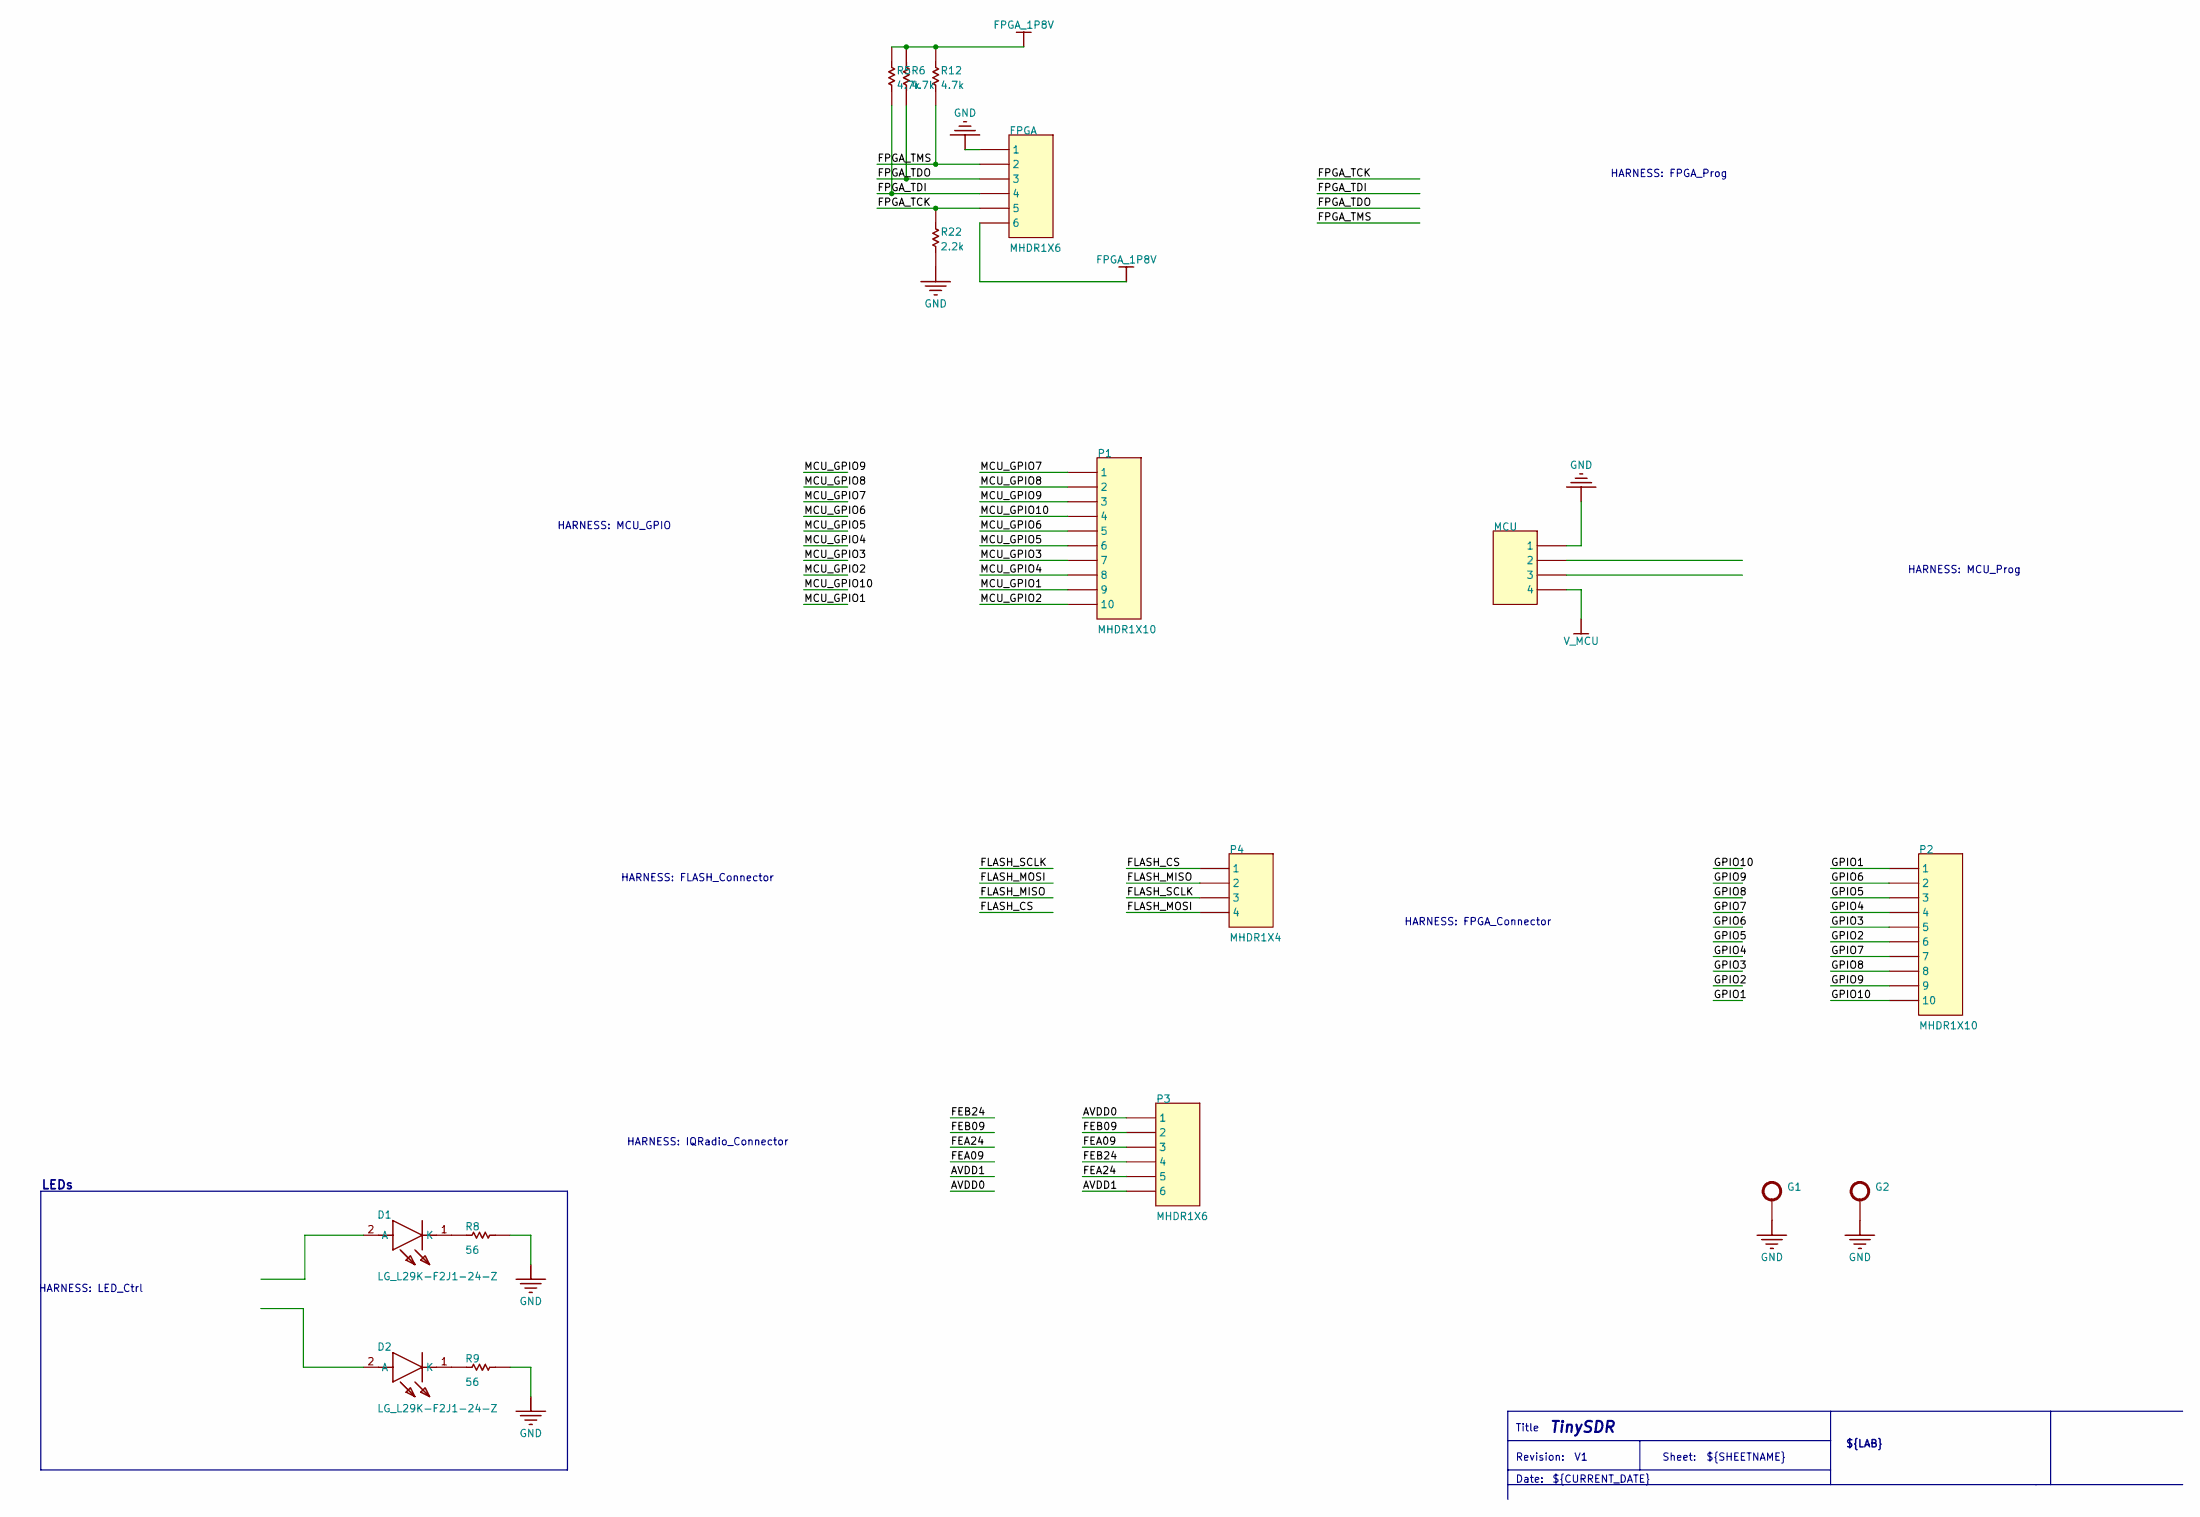
[picture p34: schematic tinysdr_Connectors.kicad_sch]

Parts:
D1, D2: LG_L29K-F2J1-24-Z; LY-L29K; MPN LG L29K-F2J1-24-Z; DIGI-KEY PART NUMBER 475-3118-1-ND
FPGA: MHDR1X6; MPN LPPB061NFFN-RC; DIGI-KEY PART NUMBER S9008E-06-ND
G1, G2: Test Point, black; Test Point - Small; RATING *; MPN 5001; DIGI-KEY PART NUMBER 36-5001-ND
MCU: MHDR1X4-angled; MHDR1X4; MPN 851-47-004-10-001000; DIGI-KEY PART NUMBER ED11256-ND
P1, P2: MHDR1X10; MPN LPPB101NFFN-RC; DIGI-KEY PART NUMBER S9008E-10-ND
P3: MHDR1X6; MPN LPPB061NFFN-RC; DIGI-KEY PART NUMBER S9008E-06-ND
P4: MHDR1X4; MPN 851-47-004-10-001000; DIGI-KEY PART NUMBER ED11256-ND
R5, R6, R12: Res; 0201; RATING *; MANUFACTURER PART NUMBER *; DIGI-KEY PART NUMBER 311-4.70KMCT-ND
R8, R9: Res; 0201; RATING *; MANUFACTURER PART NUMBER *; DIGI-KEY PART NUMBER RMCF0201JT56R0CT-ND
R22: Res; 0201; RATING *; MANUFACTURER PART NUMBER *; DIGI-KEY PART NUMBER YAG2572DKR-ND

Connections:
AVDD0: P3.1
AVDD1: P3.6
FEA09: P3.3
FEA24: P3.5
FEB09: P3.2
FEB24: P3.4
FLASH_CS: P4.1
FLASH_MISO: P4.2
FLASH_MOSI: P4.4
FLASH_SCLK: P4.3
FPGA_TCK: FPGA.5, R22.2
FPGA_TDI: FPGA.4, R5.1
FPGA_TDO: FPGA.3, R6.1
FPGA_TMS: FPGA.2, R12.1
GPIO1: P2.1
GPIO2: P2.6
GPIO3: P2.5
GPIO4: P2.4
GPIO5: P2.3
GPIO6: P2.2
GPIO7: P2.7
GPIO8: P2.8
GPIO9: P2.9
GPIO10: P2.10
MCU_GPIO1: P1.9
MCU_GPIO2: P1.10
MCU_GPIO3: P1.7
MCU_GPIO4: P1.8
MCU_GPIO5: P1.6
MCU_GPIO6: P1.5
MCU_GPIO7: P1.1
MCU_GPIO8: P1.2
MCU_GPIO9: P1.3
MCU_GPIO10: P1.4
unnamed: D1.1 (K), R8.2
unnamed: D2.1 (K), R9.2
unnamed: R5.2, R6.2, R12.2

Notes on the sheet:
${REVISION}
HARNESS: FLASH_Connector
HARNESS: LED_Ctrl
Date:
${SHEETNAME}
LEDs
Title
Revision:
${LAB}
HARNESS: FPGA_Connector
HARNESS: FPGA_Prog
${CURRENT_DATE}
HARNESS: MCU_GPIO
HARNESS: IQRadio_Connector
${TITLE}
Sheet:
HARNESS: MCU_Prog
