uw-x/tinysdr/hardware/pcb-tinysdr/tinysdr_FPGA.kicad_sch

## KiCad design hardware/pcb-tinysdr/tinysdr_FPGA.kicad_sch (2022-02-07)

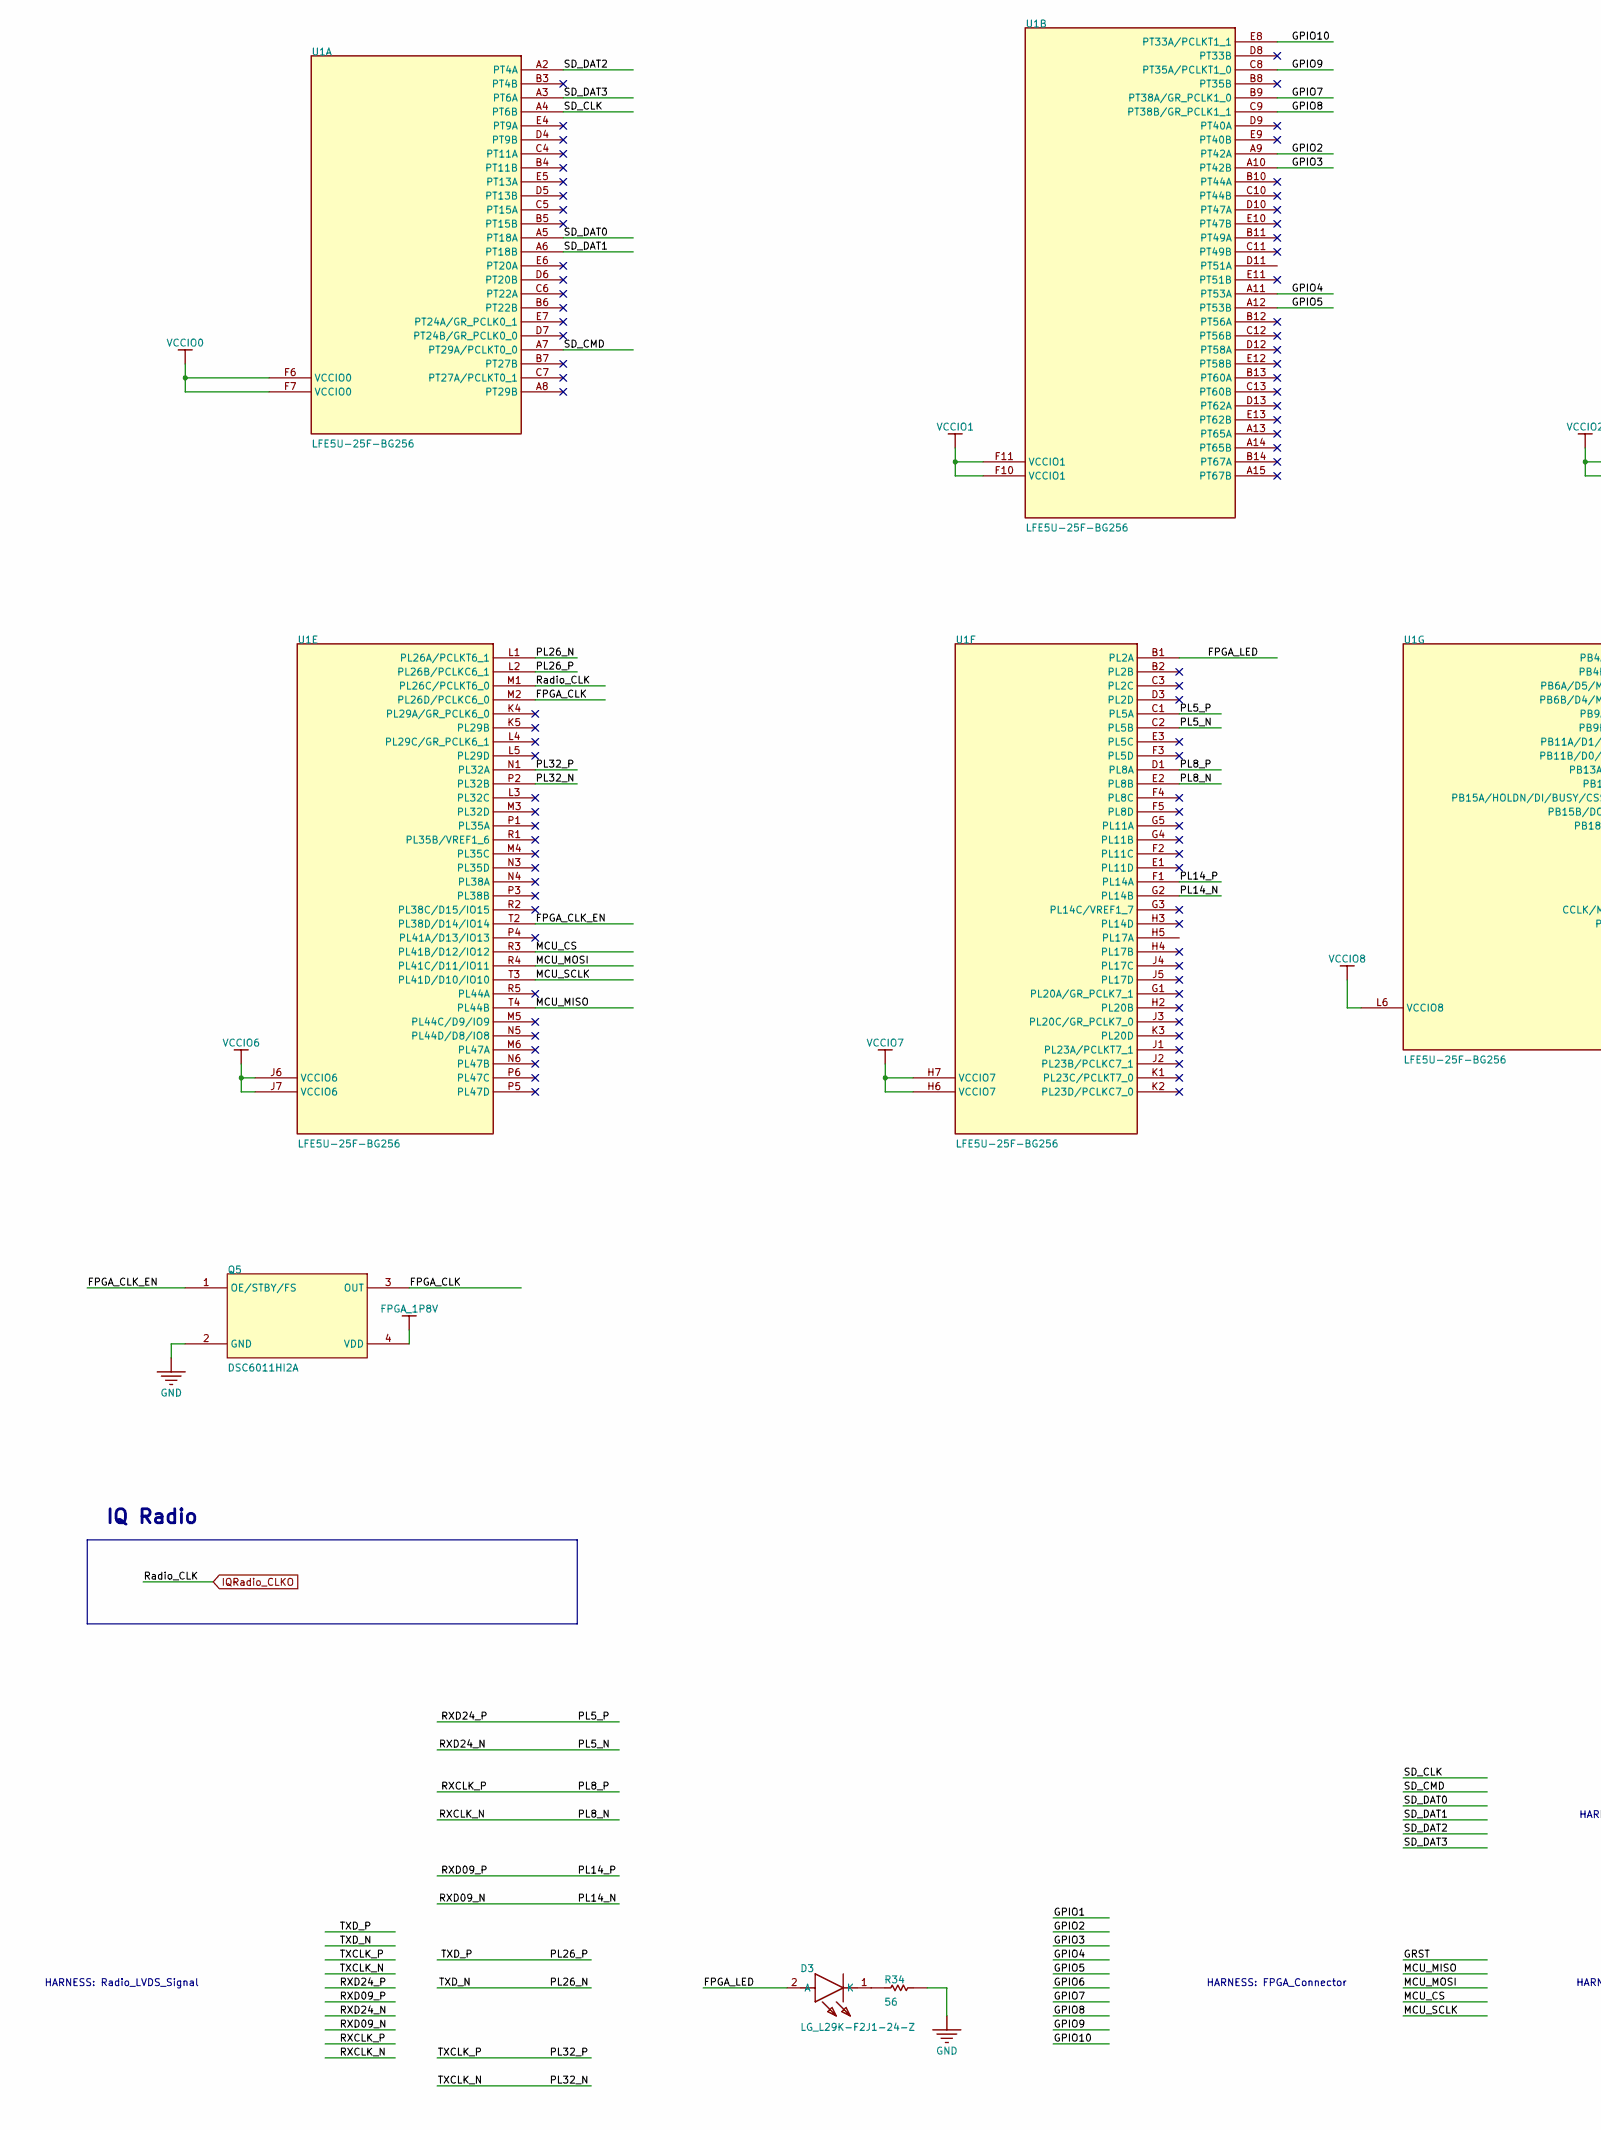
[picture p35: schematic tinysdr_FPGA.kicad_sch, part in row 1, column 1]

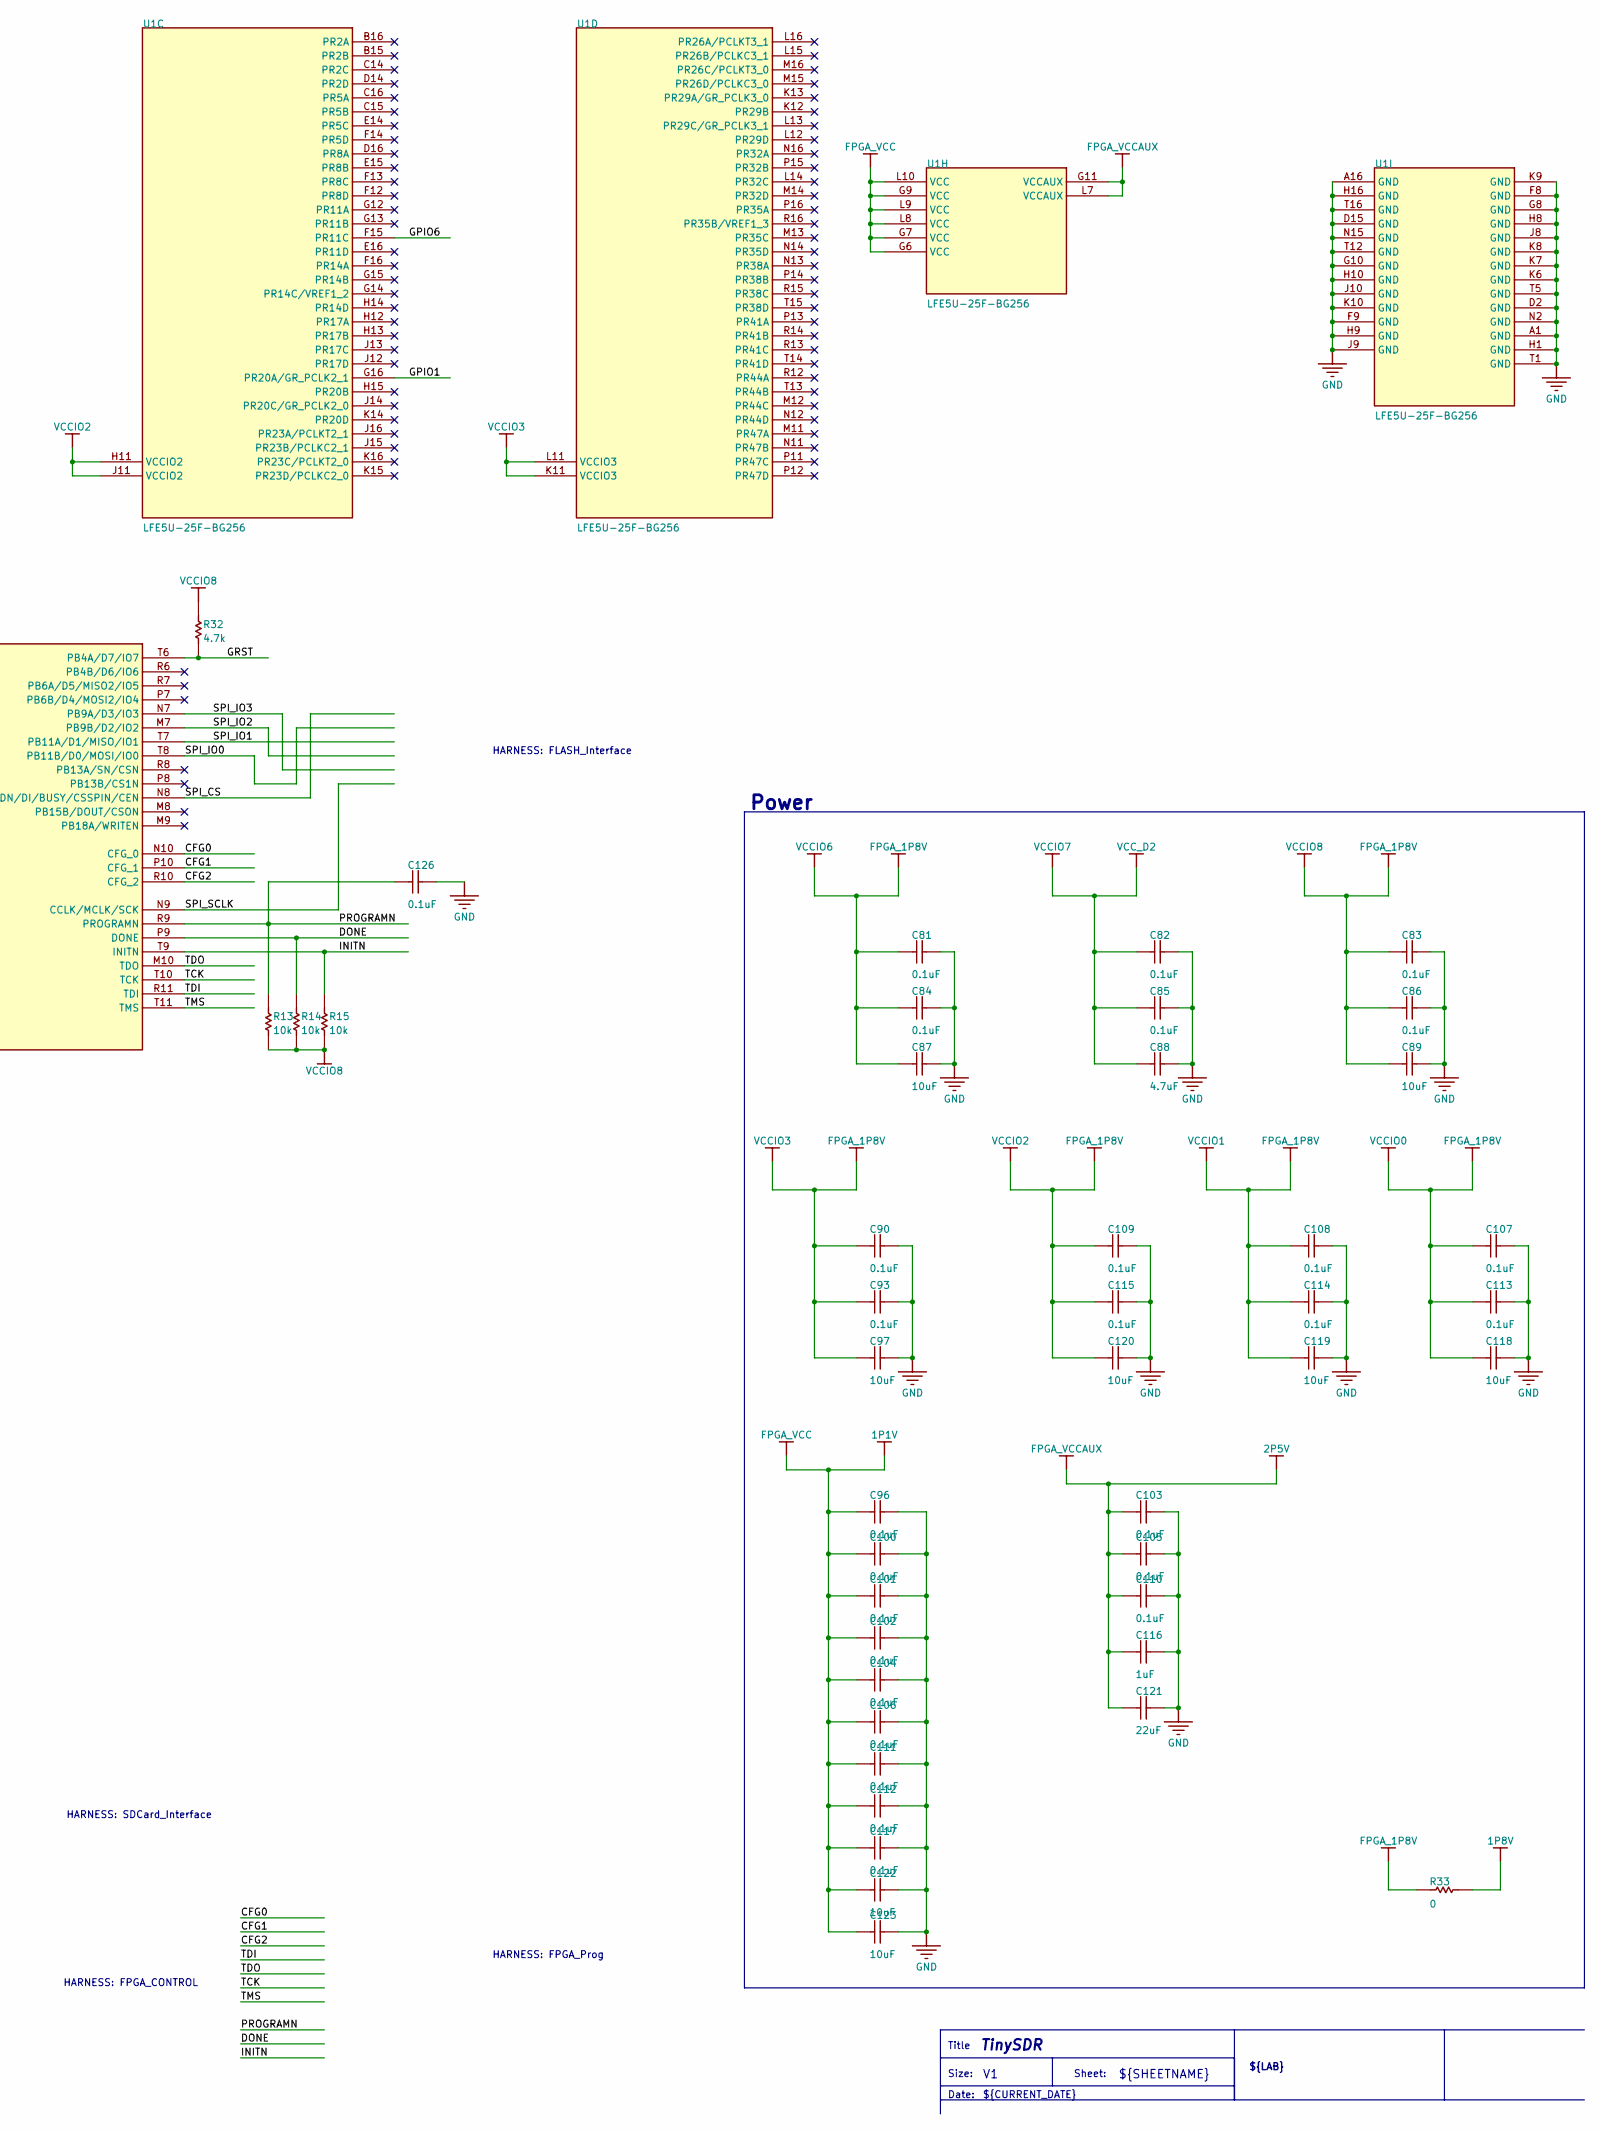
[picture p36: schematic tinysdr_FPGA.kicad_sch, part in row 1, column 2]

Parts:
C81, C82, C83, C84, C85, C86, C90, C93, C96, C100, C101, C102, C103, C104, C105, C106, C107, C108, C109, C110, C111, C112, C113, C114, C115, C117, C126: Cap; 0201; RATING *; MPN GRM033C80J104KE15D; DIGI-KEY PART NUMBER 490-10390-1-ND
C87, C89, C97, C118, C119, C120, C122, C123: Cap; 0402; RATING *; MPN GRM155R60G106ME44D; DIGI-KEY PART NUMBER 490-10693-1-ND
C88: Cap; 0201; RATING *; MPN GRM035R60J475ME15D; DIGI-KEY PART NUMBER 490-13230-1-ND
C116: Cap; 0402; RATING *; MPN GRT155C80J105KE01D; DIGI-KEY PART NUMBER 490-12233-1-ND
C121: Cap; 0603; RATING *; MPN CL10A226KQ8NRNE; DIGI-KEY PART NUMBER 1276-2867-1-ND
D3: LG_L29K-F2J1-24-Z; LY-L29K; MPN LG L29K-F2J1-24-Z; DIGI-KEY PART NUMBER 475-3118-1-ND
Q5: DSC6011HI2A; VFLGA16x12; MPN DSC6011HI2A-032.0000; DIGI-KEY PART NUMBER DSC6011HI2A-032.0000-ND
R13, R14, R15: Res; 0201; RATING *; MPN ERA-1ARB103C; DIGI-KEY PART NUMBER P121681CT-ND
R32: Res; 0201; RATING *; MPN RC0201FR-074K7L; DIGI-KEY PART NUMBER 311-4.70KMCT-ND
R33: Res; 0402; RATING *; MPN CRCW04020000Z0EDHP; DIGI-KEY PART NUMBER 541-0.0YBCT-ND
R34: Res; 0201; RATING *; MPN RMCF0201JT56R0; DIGI-KEY PART NUMBER RMCF0201JT56R0CT-ND
U1: LFE5U-25F-BG256; caBGA256; MPN LFE5U-25F-6BG256I; DIGI-KEY PART NUMBER 220-2206-ND

Connections:
CFG0: U1.N10 (CFG_0)
CFG1: U1.P10 (CFG_1)
CFG2: U1.R10 (CFG_2)
DONE: R14.2, U1.P9 (DONE)
FPGA_CLK: Q5.3 (OUT), U1.M2 (PL26D/PCLKC6_0)
FPGA_CLK_EN: Q5.1 (OE/STBY/FS), U1.T2 (PL38D/D14/IO14)
FPGA_LED: D3.2 (A), U1.B1 (PL2A)
GPIO1: U1.G16 (PR20A/GR_PCLK2_1)
GPIO2: U1.A9 (PT42A)
GPIO3: U1.A10 (PT42B)
GPIO4: U1.A11 (PT53A)
GPIO5: U1.A12 (PT53B)
GPIO6: U1.F15 (PR11C)
GPIO7: U1.B9 (PT38A/GR_PCLK1_0)
GPIO8: U1.C9 (PT38B/GR_PCLK1_1)
GPIO9: U1.C8 (PT35A/PCLKT1_0)
GPIO10: U1.E8 (PT33A/PCLKT1_1)
GRST: R32.1, U1.T6 (PB4A/D7/IO7)
INITN: R15.2, U1.T9 (INITN)
IQRadio_CLKO: U1.M1 (PL26C/PCLKT6_0)
MCU_CS: U1.R3 (PL41B/D12/IO12)
MCU_MISO: U1.T4 (PL44B)
MCU_MOSI: U1.R4 (PL41C/D11/IO11)
MCU_SCLK: U1.T3 (PL41D/D10/IO10)
unnamed: C81.1, C84.1, C87.1
unnamed: C81.2, C84.2, C87.2
unnamed: C82.1, C85.1, C88.1
unnamed: C82.2, C85.2, C88.2
unnamed: C83.1, C86.1, C89.1
unnamed: C83.2, C86.2, C89.2
unnamed: C90.1, C93.1, C97.1
unnamed: C90.2, C93.2, C97.2
unnamed: C96.1, C100.1, C101.1, C102.1, C104.1, C106.1, C111.1, C112.1, C117.1, C122.1, C123.1
unnamed: C96.2, C100.2, C101.2, C102.2, C104.2, C106.2, C111.2, C112.2, C117.2, C122.2, C123.2
unnamed: C103.1, C105.1, C110.1, C116.1, C121.1
unnamed: C103.2, C105.2, C110.2, C116.2, C121.2
unnamed: C107.1, C113.1, C118.1
unnamed: C107.2, C113.2, C118.2
unnamed: C108.1, C114.1, C119.1
unnamed: C108.2, C114.2, C119.2
unnamed: C109.1, C115.1, C120.1
unnamed: C109.2, C115.2, C120.2
unnamed: D3.1 (K), R34.2
unnamed: R13.1, R14.1, R15.1
unnamed: U1.A1 (GND), U1.D2 (GND), U1.F8 (GND), U1.G8 (GND), U1.H1 (GND), U1.H8 (GND), U1.J8 (GND), U1.K6 (GND), U1.K7 (GND), U1.K8 (GND), U1.K9 (GND), U1.N2 (GND), U1.T1 (GND), U1.T5 (GND)
unnamed: U1.A16 (GND), U1.D15 (GND), U1.F9 (GND), U1.G10 (GND), U1.H9 (GND), U1.H10 (GND), U1.H16 (GND), U1.J9 (GND), U1.J10 (GND), U1.K10 (GND), U1.N15 (GND), U1.T12 (GND), U1.T16 (GND)
unnamed: U1.F6 (VCCIO0), U1.F7 (VCCIO0)
unnamed: U1.F10 (VCCIO1), U1.F11 (VCCIO1)
unnamed: U1.G6 (VCC), U1.G7 (VCC), U1.G9 (VCC), U1.L8 (VCC), U1.L9 (VCC), U1.L10 (VCC)
unnamed: U1.G11 (VCCAUX), U1.L7 (VCCAUX)
unnamed: U1.H6 (VCCIO7), U1.H7 (VCCIO7)
unnamed: U1.H11 (VCCIO2), U1.J11 (VCCIO2)
unnamed: U1.J6 (VCCIO6), U1.J7 (VCCIO6)
unnamed: U1.K11 (VCCIO3), U1.L11 (VCCIO3)
PL5_N: U1.C2 (PL5B)
PL5_P: U1.C1 (PL5A)
PL8_N: U1.E2 (PL8B)
PL8_P: U1.D1 (PL8A)
PL14_N: U1.G2 (PL14B)
PL14_P: U1.F1 (PL14A)
PL26_N: U1.L1 (PL26A/PCLKT6_1)
PL26_P: U1.L2 (PL26B/PCLKC6_1)
PL32_N: U1.P2 (PL32B)
PL32_P: U1.N1 (PL32A)
PROGRAMN: C126.1, R13.2, U1.R9 (PROGRAMN)
SD_CLK: U1.A4 (PT6B)
SD_CMD: U1.A7 (PT29A/PCLKT0_0)
SD_DAT0: U1.A5 (PT18A)
SD_DAT1: U1.A6 (PT18B)
SD_DAT2: U1.A2 (PT4A)
SD_DAT3: U1.A3 (PT6A)
SPI_CS: U1.N8 (PB15A/HOLDN/DI/BUSY/CSSPIN/CEN)
SPI_IO0: U1.T8 (PB11B/D0/MOSI/IO0)
SPI_IO1: U1.T7 (PB11A/D1/MISO/IO1)
SPI_IO2: U1.M7 (PB9B/D2/IO2)
SPI_IO3: U1.N7 (PB9A/D3/IO3)
SPI_SCLK: U1.N9 (CCLK/MCLK/SCK)
TCK: U1.T10 (TCK)
TDI: U1.R11 (TDI)
TDO: U1.M10 (TDO)
TMS: U1.T11 (TMS)

Notes on the sheet:
HARNESS: FPGA_Prog
${SHEETNAME}
${CURRENT_DATE}
${LAB}
IQ Radio
${TITLE}
Sheet:
Size:
HARNESS: Radio_LVDS_Signal
HARNESS: FPGA_CONTROL
HARNESS: FLASH_Interface
Date:
${REVISION}
HARNESS: FPGA_Connector
HARNESS: SDCard_Interface
Power
Title
