uw-x/tinysdr/hardware/pcb-tinysdr/tinysdr_IQ_Radio.kicad_sch

## KiCad design hardware/pcb-tinysdr/tinysdr_IQ_Radio.kicad_sch (2022-02-07)

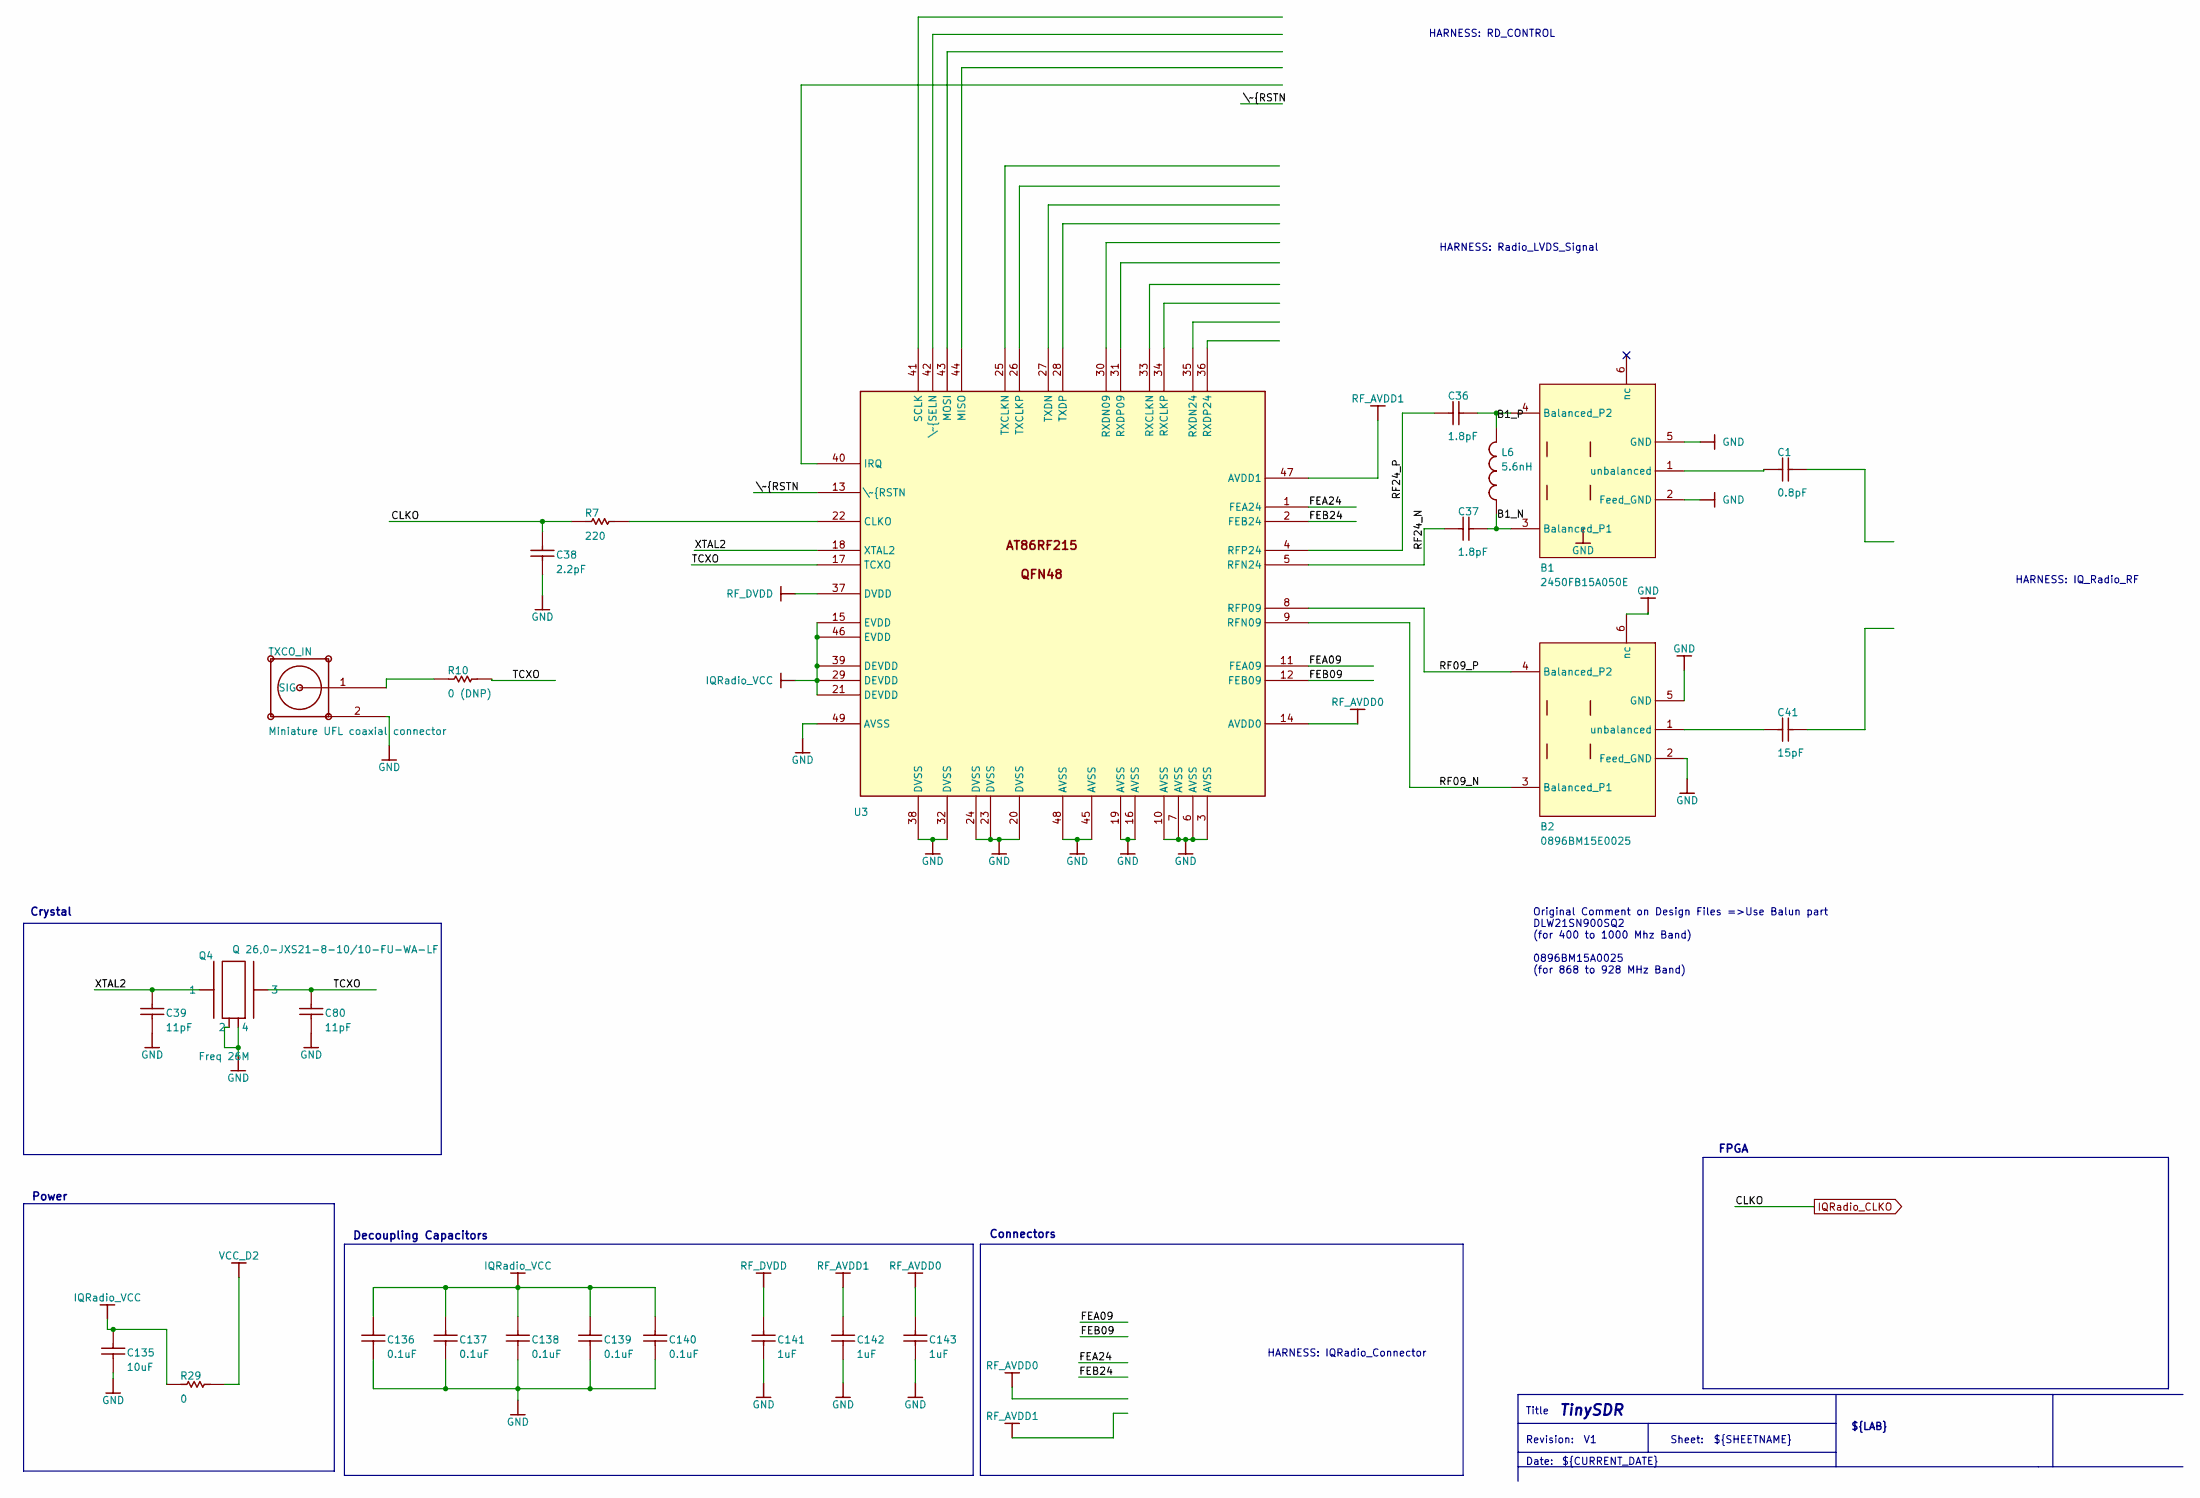
[picture p37: schematic tinysdr_IQ_Radio.kicad_sch]

Parts:
B1: Balun_2.4GHz; FIL_0910CF15B0100E; PARTGROUP Inductors,RF,Other RF; DIGI-KEY PART NUMBER 712-1065-1-ND
B2: Balun_2.4GHz; XFMR_B0310J50100AHF; PARTGROUP Inductors,RF,Other RF; DIGI-KEY PART NUMBER 712-1590-1-ND
C1: Cap; 0201; RATING *; MANUFACTURER PART NUMBER *; DIGI-KEY PART NUMBER 490-6111-1-ND
C36, C37: Cap; 0201; RATING *; MPN GRM0335C1H1R8CA01D; DIGI-KEY PART NUMBER 490-11314-1-ND
C38: Cap; 0201; RATING *; MPN GRM0335C1H2R2CA01D; DIGI-KEY PART NUMBER 490-6125-1-ND
C39, C80: Cap; 0201; RATING *; MPN CAP CER 11PF 25V C0G/NP0 0201; DIGI-KEY PART NUMBER 712-1206-6-ND
C41: Cap; 0201; RATING *; MANUFACTURER PART NUMBER *; DIGI-KEY PART NUMBER 490-9658-1-ND
C135: Cap; 0603; RATING *; MPN CL10A106MQ8NNNC; DIGI-KEY PART NUMBER 1276-1119-1-ND
C136, C137, C138, C139, C140: Cap; 0201; RATING *; MPN GRM033C71C104KE14D; DIGI-KEY PART NUMBER 490-10387-1-ND
C141, C142, C143: Cap; 0201; RATING *; MPN GRM033R60J105MEA2D; DIGI-KEY PART NUMBER 490-7229-1-ND
L6: Ind; _work_pcb_xsdr_v2_Libraries_WREL_AD10_Ben.PcbLib_0201; RATING *; MANUFACTURER PART NUMBER *; DIGI-KEY PART NUMBER 712-1500-1-ND
Q4: Q 26,0-JXS21-8-10/10-FU-WA-LF; Q 26,0-JXS21-8-10{slash}10-FU-WA-LF; MPN Q 26,0-JXS21-8-10/10-FU-WA-LF; DIGI-KEY PART NUMBER 1908-1164-1-ND
R7: Res; 0201; RATING *; MANUFACTURER PART NUMBER *; DIGI-KEY PART NUMBER 311-220NCT-ND
R10: Res; 0402; RATING *; MANUFACTURER PART NUMBER *
R29: Res; 0402; RATING *; MANUFACTURER PART NUMBER *; DIGI-KEY PART NUMBER 541-0.0YBCT-ND
TXCO_IN: Miniature UFL coaxial connector; UFL Connector; MPN 1909763-1; DIGI-KEY PART NUMBER A118077CT-ND
U3: 48 lead QFN package; QFN50P700X700X90-49N; PARTGROUP Integrated Circuits,Interface ICs,RF; DIGI-KEY PART NUMBER AT86RF215-ZU-ND

Connections:
B1_N: B1.3 (Balanced_P1), C37.2, L6.1
B1_P: B1.4 (Balanced_P2), C36.2, L6.2
FEA09: U3.11 (FEA09)
FEA24: U3.1 (FEA24)
FEB09: U3.12 (FEB09)
FEB24: U3.2 (FEB24)
IQRadio_CLKO: C38.2, R7.2
unnamed: B1.1 (unbalanced), C1.1
unnamed: B2.1 (unbalanced), C41.1
unnamed: C135.1, R29.1
unnamed: C136.1, C137.1, C138.1, C139.1, C140.1
unnamed: C136.2, C137.2, C138.2, C139.2, C140.2
unnamed: Q4.2, Q4.4
unnamed: R7.1, U3.22 (CLKO)
unnamed: R10.2, TXCO_IN.1 (SIG)
unnamed: U3.3 (AVSS), U3.6 (AVSS), U3.7 (AVSS), U3.10 (AVSS)
unnamed: U3.15 (EVDD), U3.21 (DEVDD), U3.29 (DEVDD), U3.39 (DEVDD), U3.46 (EVDD)
unnamed: U3.16 (AVSS), U3.19 (AVSS)
unnamed: U3.20 (DVSS), U3.23 (DVSS), U3.24 (DVSS)
unnamed: U3.32 (DVSS), U3.38 (DVSS)
unnamed: U3.45 (AVSS), U3.48 (AVSS)
RF09_N: B2.3 (Balanced_P1), U3.9 (RFN09)
RF09_P: B2.4 (Balanced_P2), U3.8 (RFP09)
RF24_N: C37.1, U3.5 (RFN24)
RF24_P: C36.1, U3.4 (RFP24)
TCXO: C80.2, Q4.3, R10.1, U3.17 (TCXO)
XTAL2: C39.2, Q4.1, U3.18 (XTAL2)
\~{RSTN: U3.13 (\~{RSTN)

Notes on the sheet:
Decoupling Capacitors
Date:
FPGA
HARNESS: RD_CONTROL
HARNESS: Radio_LVDS_Signal
Sheet:
Crystal
${TITLE}
Title
HARNESS: IQ_Radio_RF
Power
${SHEETNAME}
Revision:
Original Comment on Design Files =>Use Balun part DLW21SN900SQ2 (for 400 to 1000 Mhz Band) 0896BM15A0025 (for 868 to 928 MHz Band)
HARNESS: IQRadio_Connector
Connectors
${REVISION}
${LAB}
${CURRENT_DATE}
