uw-x/tinysdr/hardware/pcb-tinysdr/tinysdr_MCU.kicad_sch

## KiCad design hardware/pcb-tinysdr/tinysdr_MCU.kicad_sch (2022-02-07)

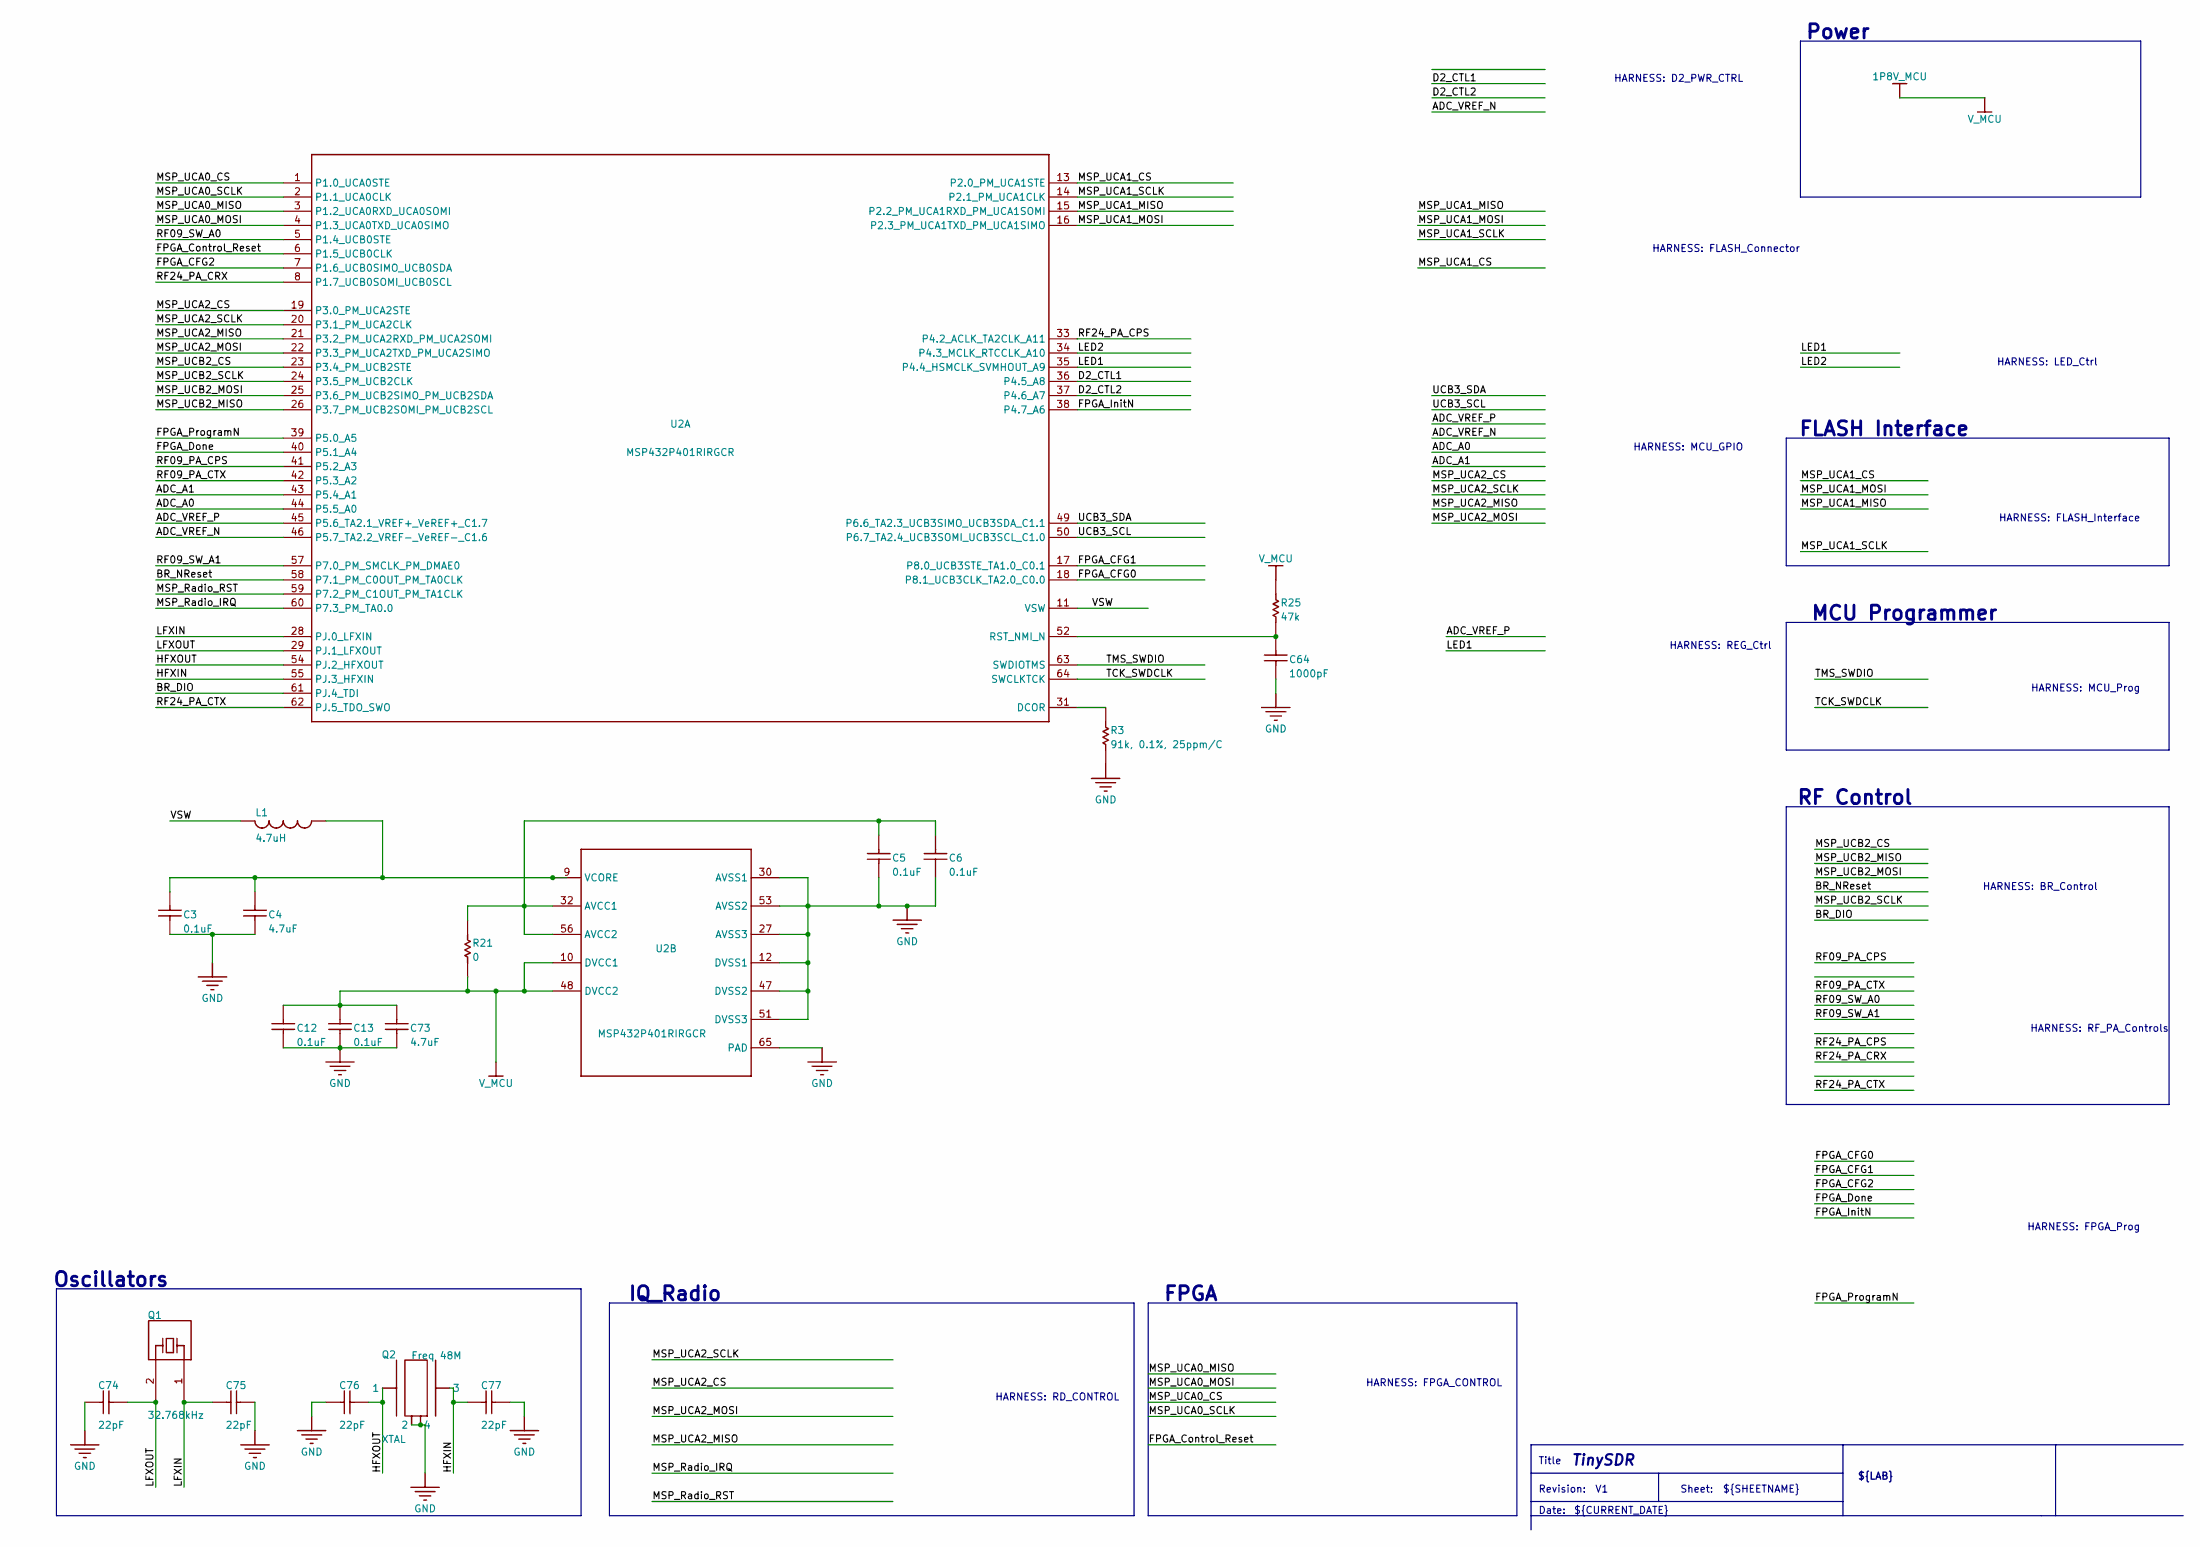
[picture p38: schematic tinysdr_MCU.kicad_sch]

Parts:
C3: Cap; 0201; RATING *; MPN GRM033C71C104KE14D; DIGI-KEY PART NUMBER 490-10387-1-ND
C4: Cap; 0201; RATING *; MPN GRM035R60J475ME15D; DIGI-KEY PART NUMBER 490-13230-1-ND
C5, C6, C12, C13: Cap; 0201; RATING *; MANUFACTURER PART NUMBER *; DIGI-KEY PART NUMBER 490-10387-1-ND
C64: Cap; 0201; RATING *; MANUFACTURER PART NUMBER *; DIGI-KEY PART NUMBER 490-3184-1-ND
C73: Cap; 0201; RATING *; MANUFACTURER PART NUMBER *; DIGI-KEY PART NUMBER 490-13230-1-ND
C74, C75, C76, C77: Cap; 0201; RATING *; MANUFACTURER PART NUMBER *; DIGI-KEY PART NUMBER 490-6123-1-ND
L1: Ind; 0603; RATING *; MANUFACTURER PART NUMBER *; DIGI-KEY PART NUMBER 445-6390-1-ND
Q1: XTAL; XTAL [2.00mm x 1.20mm]; MANUFACTURER PART NUMBER FC-135 32.7680KA-A3; DIGI-KEY PART NUMBER CTX1455CT-ND
Q2: XTAL; CX2016DB48000H0FLJC1; MPN CX2016DB48000H0FLJC1; DIGI-KEY PART NUMBER 1253-1712-1-ND
R3: Res; 0201; RATING *; MANUFACTURER PART NUMBER *; DIGI-KEY PART NUMBER YAG2842CT-ND
R21: Res; 0201; RATING *; MANUFACTURER PART NUMBER *; DIGI-KEY PART NUMBER P15979CT-ND
R25: Res; 0201; RATING *; MANUFACTURER PART NUMBER *; DIGI-KEY PART NUMBER 1276-3701-1-ND
U2: MSP432P401RIRGCR; RGC0064B; PARTNUMBER MSP432P401RIRGCR; DIGI-KEY PART NUMBER 296-45565-1-ND

Connections:
ADC_A0: U2.44 (P5.5_A0)
ADC_A1: U2.43 (P5.4_A1)
ADC_VREF_N: U2.46 (P5.7_TA2.2_VREF-_VeREF-_C1.6)
ADC_VREF_P: U2.45 (P5.6_TA2.1_VREF+_VeREF+_C1.7)
BR_DIO: U2.61 (PJ.4_TDI)
BR_NReset: U2.58 (P7.1_PM_C0OUT_PM_TA0CLK)
D2_CTL1: U2.36 (P4.5_A8)
D2_CTL2: U2.37 (P4.6_A7)
FPGA_CFG0: U2.18 (P8.1_UCB3CLK_TA2.0_C0.0)
FPGA_CFG1: U2.17 (P8.0_UCB3STE_TA1.0_C0.1)
FPGA_CFG2: U2.7 (P1.6_UCB0SIMO_UCB0SDA)
FPGA_Control_Reset: U2.6 (P1.5_UCB0CLK)
FPGA_Done: U2.40 (P5.1_A4)
FPGA_InitN: U2.38 (P4.7_A6)
FPGA_ProgramN: U2.39 (P5.0_A5)
HFXIN: C77.2, Q2.3, U2.55 (PJ.3_HFXIN)
HFXOUT: C76.1, Q2.1, U2.54 (PJ.2_HFXOUT)
LED1: U2.35 (P4.4_HSMCLK_SVMHOUT_A9)
LED2: U2.34 (P4.3_MCLK_RTCCLK_A10)
LFXIN: C75.2, Q1.1, U2.28 (PJ.0_LFXIN)
LFXOUT: C74.1, Q1.2, U2.29 (PJ.1_LFXOUT)
MSP_Radio_IRQ: U2.60 (P7.3_PM_TA0.0)
MSP_Radio_RST: U2.59 (P7.2_PM_C1OUT_PM_TA1CLK)
MSP_UCA0_CS: U2.1 (P1.0_UCA0STE)
MSP_UCA0_MISO: U2.3 (P1.2_UCA0RXD_UCA0SOMI)
MSP_UCA0_MOSI: U2.4 (P1.3_UCA0TXD_UCA0SIMO)
MSP_UCA0_SCLK: U2.2 (P1.1_UCA0CLK)
MSP_UCA1_CS: U2.13 (P2.0_PM_UCA1STE)
MSP_UCA1_MISO: U2.15 (P2.2_PM_UCA1RXD_PM_UCA1SOMI)
MSP_UCA1_MOSI: U2.16 (P2.3_PM_UCA1TXD_PM_UCA1SIMO)
MSP_UCA1_SCLK: U2.14 (P2.1_PM_UCA1CLK)
MSP_UCA2_CS: U2.19 (P3.0_PM_UCA2STE)
MSP_UCA2_MISO: U2.21 (P3.2_PM_UCA2RXD_PM_UCA2SOMI)
MSP_UCA2_MOSI: U2.22 (P3.3_PM_UCA2TXD_PM_UCA2SIMO)
MSP_UCA2_SCLK: U2.20 (P3.1_PM_UCA2CLK)
MSP_UCB2_CS: U2.23 (P3.4_PM_UCB2STE)
MSP_UCB2_MISO: U2.26 (P3.7_PM_UCB2SOMI_PM_UCB2SCL)
MSP_UCB2_MOSI: U2.25 (P3.6_PM_UCB2SIMO_PM_UCB2SDA)
MSP_UCB2_SCLK: U2.24 (P3.5_PM_UCB2CLK)
unnamed: C3.1, C4.1
unnamed: C3.2, C4.2, L1.1, U2.9 (VCORE)
unnamed: C5.1, C6.1, U2.12 (DVSS1), U2.27 (AVSS3), U2.30 (AVSS1), U2.47 (DVSS2), U2.51 (DVSS3), U2.53 (AVSS2)
unnamed: C5.2, C6.2, R21.2, U2.32 (AVCC1), U2.56 (AVCC2)
unnamed: C12.1, C13.1, C73.1
unnamed: C12.2, C13.2, C73.2, R21.1, U2.10 (DVCC1), U2.48 (DVCC2)
unnamed: C64.2, R25.2, U2.52 (RST_NMI_N)
unnamed: Q2.2, Q2.4
unnamed: R3.2, U2.31 (DCOR)
RF09_PA_CPS: U2.41 (P5.2_A3)
RF09_PA_CTX: U2.42 (P5.3_A2)
RF09_SW_A0: U2.5 (P1.4_UCB0STE)
RF09_SW_A1: U2.57 (P7.0_PM_SMCLK_PM_DMAE0)
RF24_PA_CPS: U2.33 (P4.2_ACLK_TA2CLK_A11)
RF24_PA_CRX: U2.8 (P1.7_UCB0SOMI_UCB0SCL)
RF24_PA_CTX: U2.62 (PJ.5_TDO_SWO)
TCK_SWDCLK: U2.64 (SWCLKTCK)
TMS_SWDIO: U2.63 (SWDIOTMS)
UCB3_SCL: U2.50 (P6.7_TA2.4_UCB3SOMI_UCB3SCL_C1.0)
UCB3_SDA: U2.49 (P6.6_TA2.3_UCB3SIMO_UCB3SDA_C1.1)
VSW: L1.2, U2.11 (VSW)

Notes on the sheet:
${LAB}
Revision:
HARNESS: FPGA_Prog
${CURRENT_DATE}
Sheet:
HARNESS: FLASH_Connector
HARNESS: RD_CONTROL
RF Control
Power
${REVISION}
HARNESS: REG_Ctrl
Title
HARNESS: FPGA_CONTROL
HARNESS: FLASH_Interface
HARNESS: D2_PWR_CTRL
HARNESS: LED_Ctrl
${SHEETNAME}
HARNESS: BR_Control
IQ_Radio
HARNESS: MCU_GPIO
FPGA
FLASH Interface
HARNESS: MCU_Prog
MCU Programmer
Oscillators
${TITLE}
Date:
HARNESS: RF_PA_Controls
