uw-x/tinysdr/hardware/pcb-tinysdr/tinysdr_Memories.kicad_sch

## KiCad design hardware/pcb-tinysdr/tinysdr_Memories.kicad_sch (2022-02-07)

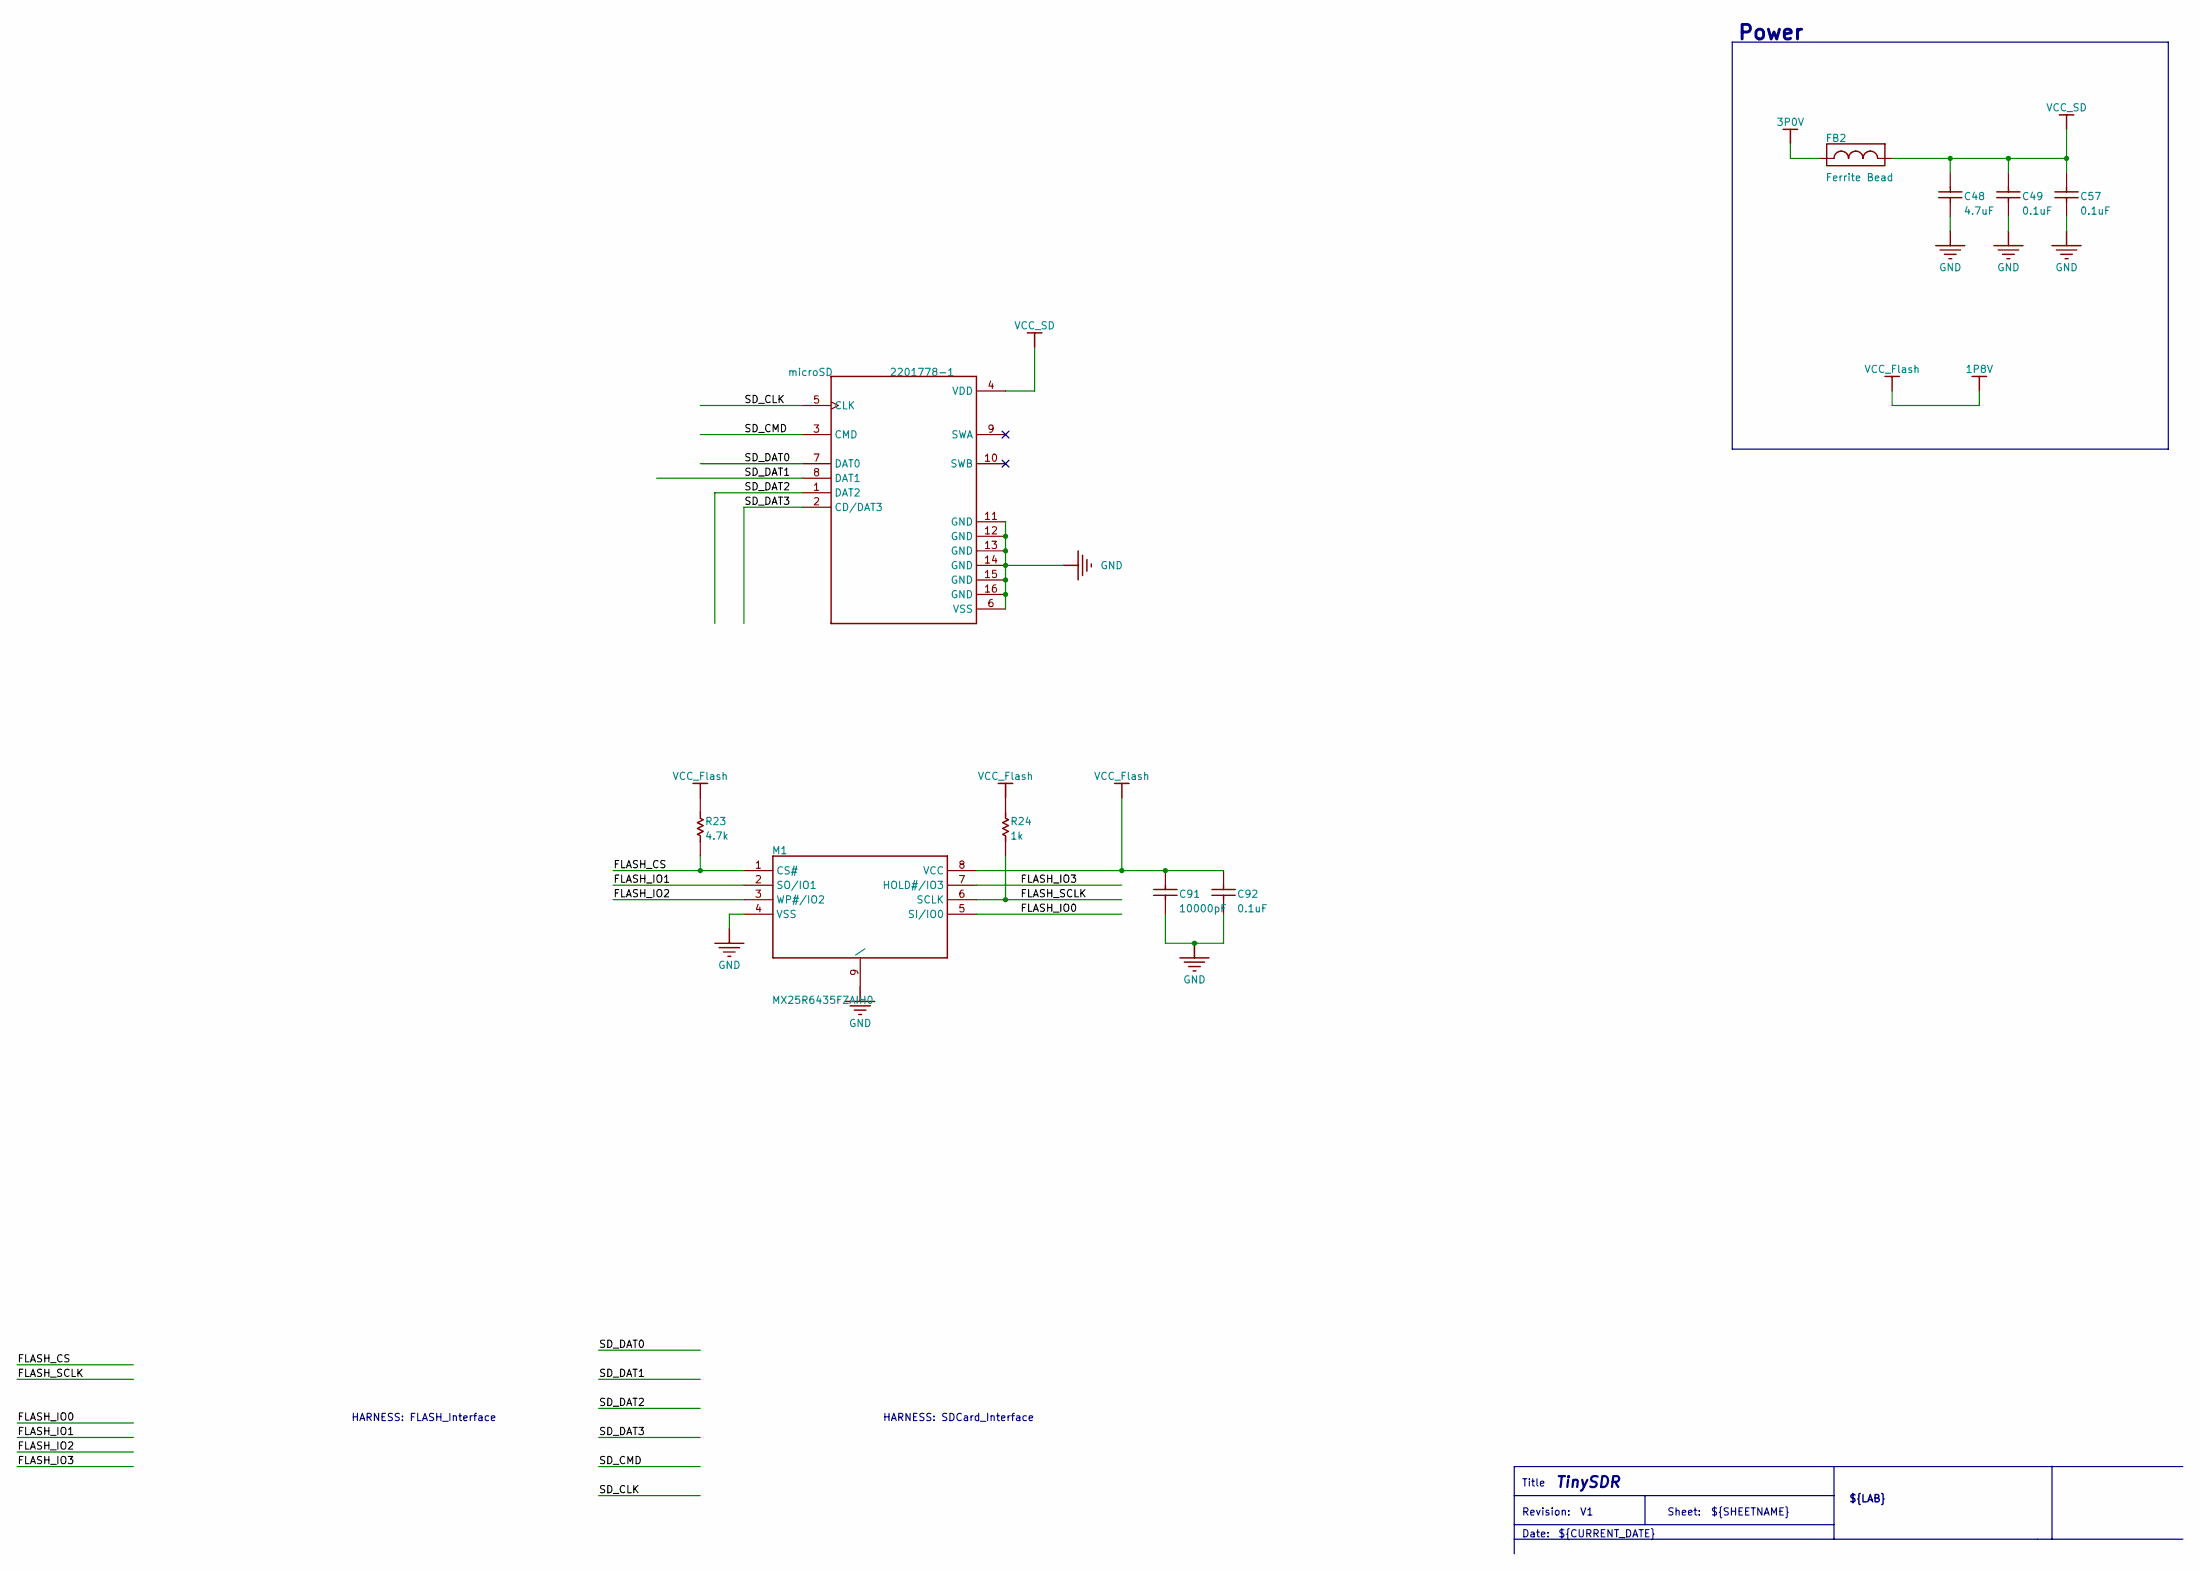
[picture p39: schematic tinysdr_Memories.kicad_sch]

Parts:
C48: Cap; 0201; RATING *; MANUFACTURER PART NUMBER *; DIGI-KEY PART NUMBER 490-13230-1-ND
C49, C57, C92: Cap; 0201; RATING *; MANUFACTURER PART NUMBER *; DIGI-KEY PART NUMBER 490-10387-1-ND
C91: Cap; 0201; RATING *; MANUFACTURER PART NUMBER *; DIGI-KEY PART NUMBER 490-7194-1-ND
FB2: Ferrite Bead; 0201; RATING *; MPN BKH0603HL221-T; DIGI-KEY PART NUMBER 587-5413-1-ND
M1: MX25R6435FZAIH0; SON80P400X400X60-9N; MPN S25FL064LABNFI043; DIGI-KEY PART NUMBER 428-4075-1-ND
R23: Res; 0201; RATING *; MANUFACTURER PART NUMBER *; DIGI-KEY PART NUMBER 311-4.70KMCT-ND
R24: Res; 0201; RATING *; MANUFACTURER PART NUMBER *; DIGI-KEY PART NUMBER 311-1KMCT-ND
microSD: 2201778-1; TE_2201778-1; MPN 2201778-1; DIGI-KEY PART NUMBER A118117CT-ND

Connections:
FLASH_CS: M1.1 (CS#), R23.1
FLASH_IO0: M1.5 (SI/IO0)
FLASH_IO1: M1.2 (SO/IO1)
FLASH_IO2: M1.3 (WP#/IO2)
FLASH_IO3: M1.7 (HOLD#/IO3)
FLASH_SCLK: M1.6 (SCLK), R24.1
unnamed: C48.2, C49.2, C57.2, FB2.2
unnamed: C91.1, C92.1
unnamed: C91.2, C92.2, M1.8 (VCC)
unnamed: microSD.6 (VSS), microSD.11 (GND), microSD.12 (GND), microSD.13 (GND), microSD.14 (GND), microSD.15 (GND), microSD.16 (GND)
SD_CLK: microSD.5 (CLK)
SD_CMD: microSD.3 (CMD)
SD_DAT0: microSD.7 (DAT0)
SD_DAT1: microSD.8 (DAT1)
SD_DAT2: microSD.1 (DAT2)
SD_DAT3: microSD.2 (CD/DAT3)

Notes on the sheet:
Sheet:
Revision:
Title
Power
${LAB}
${REVISION}
${TITLE}
HARNESS: FLASH_Interface
${SHEETNAME}
Date:
HARNESS: SDCard_Interface
${CURRENT_DATE}
