uw-x/tinysdr/hardware/pcb-tinysdr/tinysdr_Power.kicad_sch

## KiCad design hardware/pcb-tinysdr/tinysdr_Power.kicad_sch (2022-02-07)

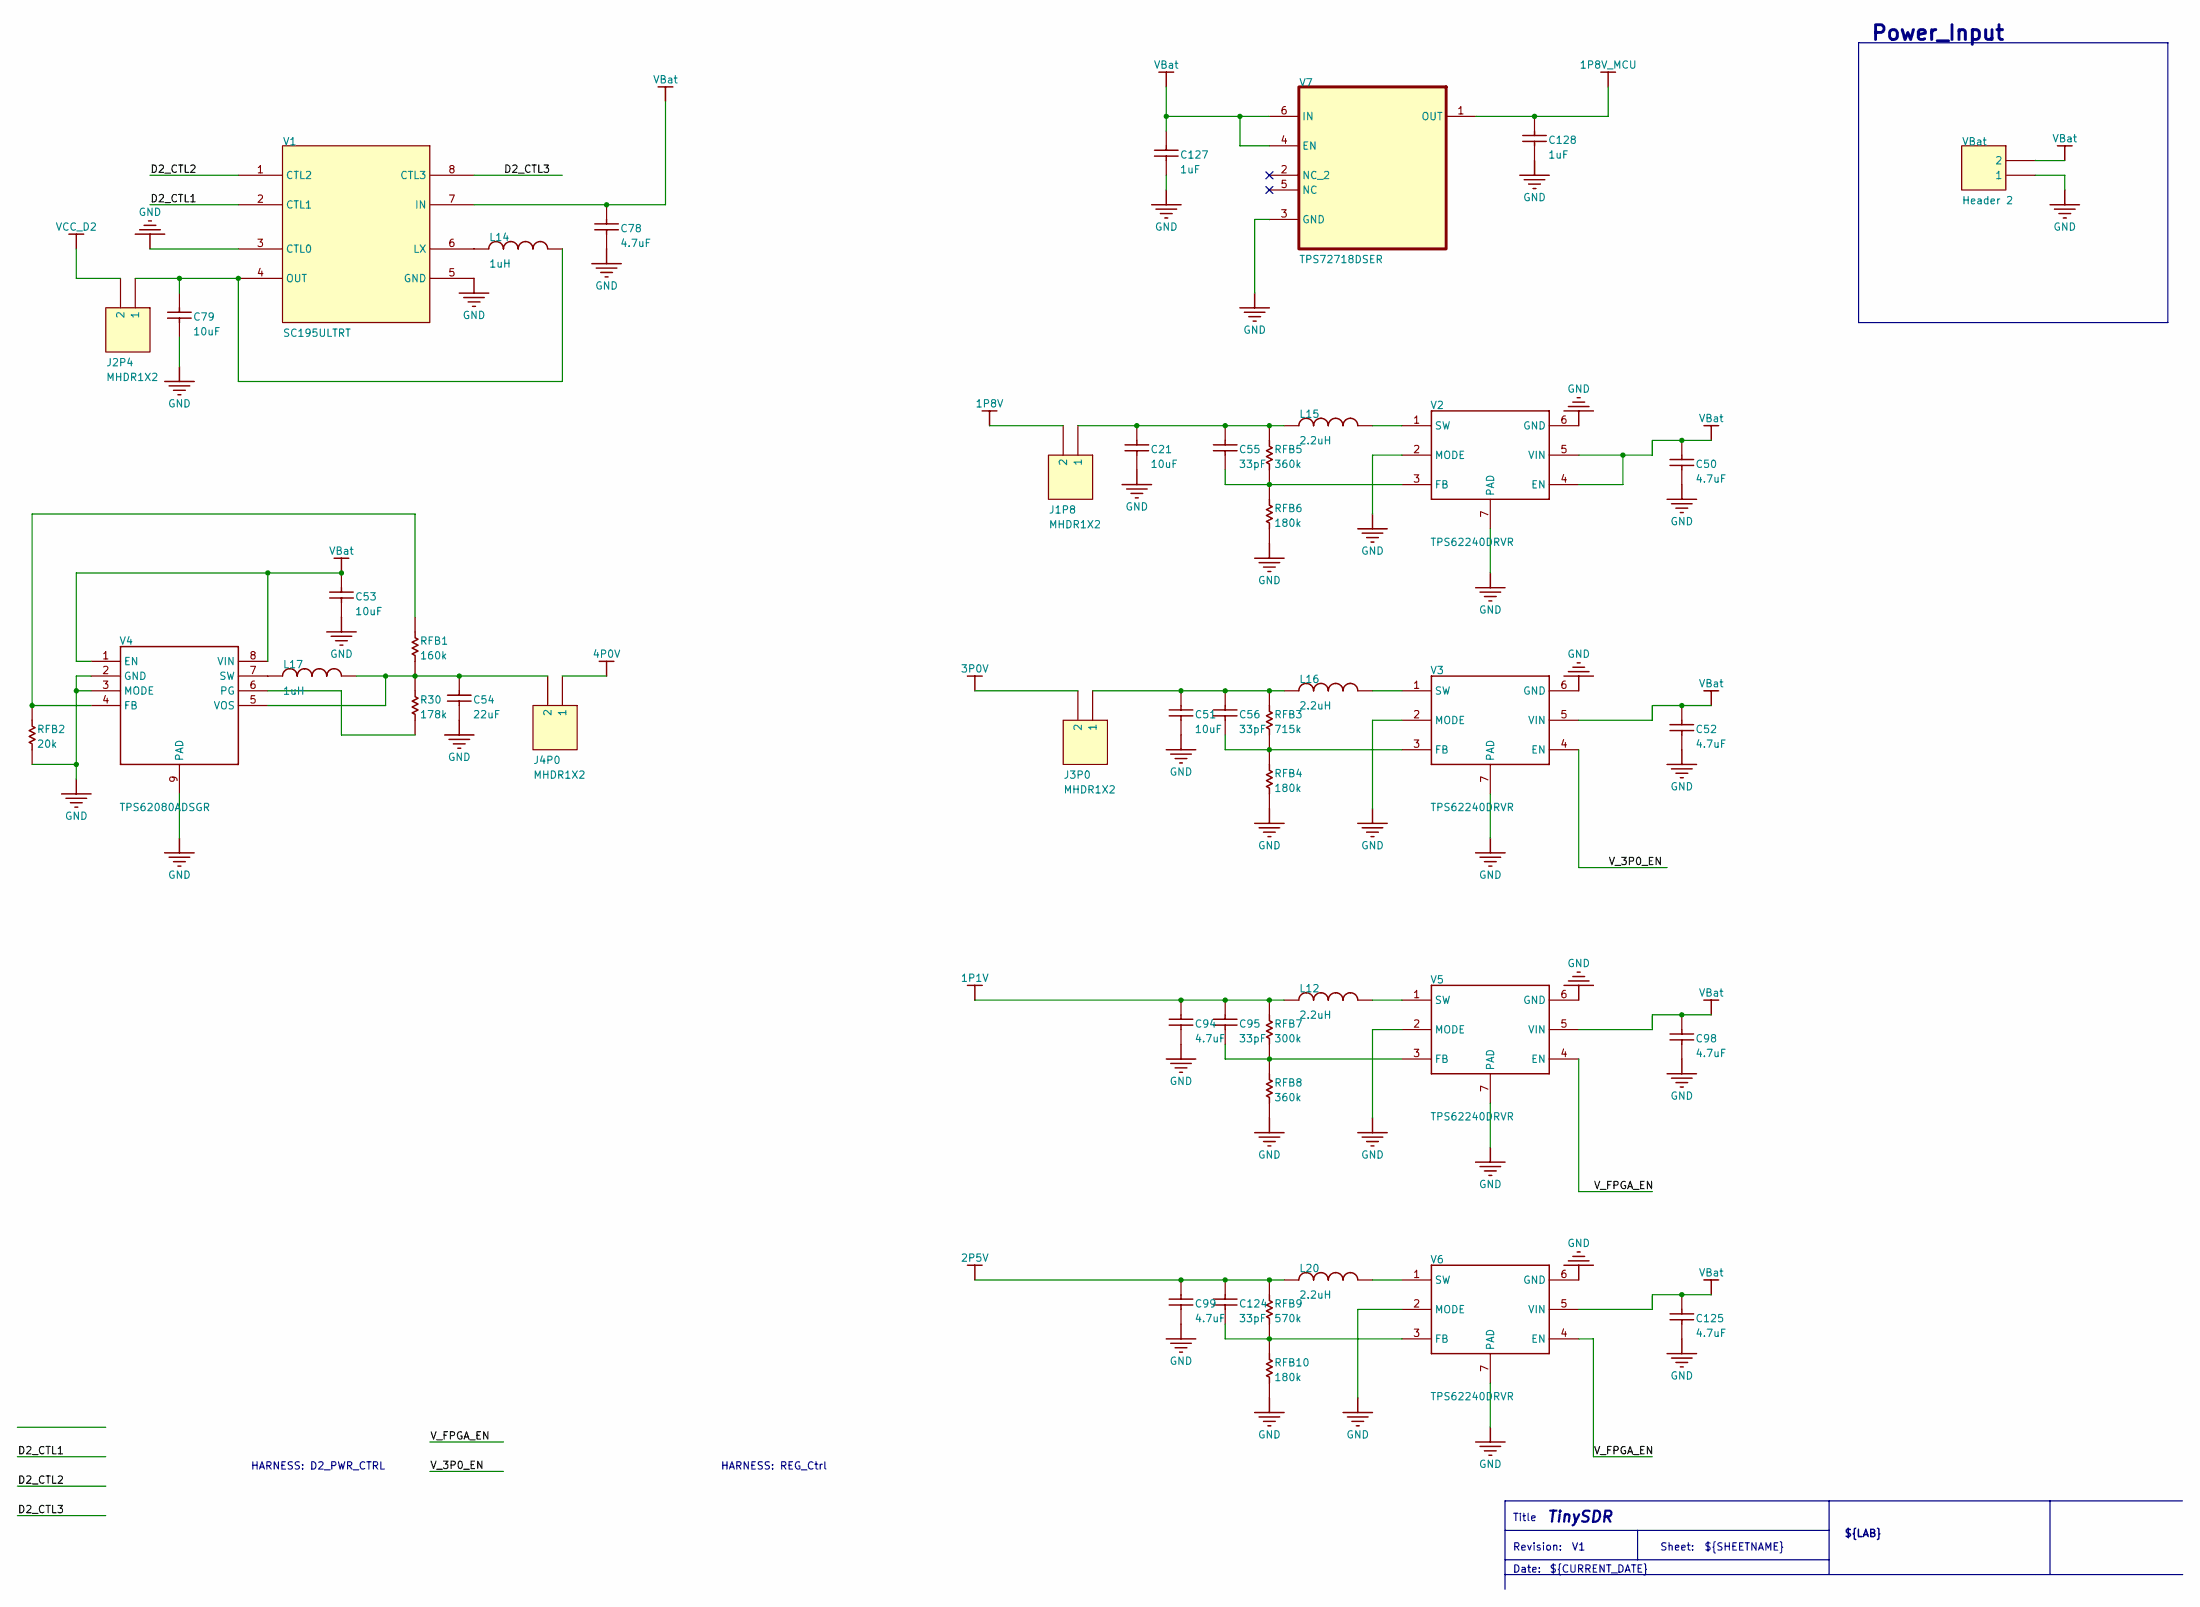
[picture p40: schematic tinysdr_Power.kicad_sch]

Parts:
C21, C51, C53, C79: Cap; 0603; RATING *; MANUFACTURER PART NUMBER *; DIGI-KEY PART NUMBER 1276-1119-1-ND
C50, C52, C78: Cap; 0603; RATING *; MANUFACTURER PART NUMBER *; DIGI-KEY PART NUMBER 1276-1907-1-ND
C54: Cap; 0603; RATING *; MANUFACTURER PART NUMBER *; DIGI-KEY PART NUMBER 1276-2867-1-ND
C55, C56, C95, C124: Cap; 0201; RATING *; MANUFACTURER PART NUMBER *; DIGI-KEY PART NUMBER 490-6126-1-ND
C94, C98, C99, C125: Cap; 0201; RATING *; MANUFACTURER PART NUMBER *; DIGI-KEY PART NUMBER 490-13230-1-ND
C127, C128: Cap; 0402; RATING *; MANUFACTURER PART NUMBER *; DIGI-KEY PART NUMBER 1276-1119-1-ND
J1P8, J2P4, J3P0, J4P0: MHDR1X2; MPN GRPB021VWVN-RC; DIGI-KEY PART NUMBER S9014E-02-ND
L12, L15, L16, L20: Ind; 0402; RATING *; MANUFACTURER PART NUMBER *; DIGI-KEY PART NUMBER 587-5908-1-ND
L14, L17: Ind; 0402; RATING *; MANUFACTURER PART NUMBER *; DIGI-KEY PART NUMBER 587-5265-6-ND
R30: Res; 0201; RATING *; MANUFACTURER PART NUMBER *; DIGI-KEY PART NUMBER YAG2443CT-ND
RFB1: Res; 0201; RATING *; MANUFACTURER PART NUMBER *; DIGI-KEY PART NUMBER YAG2426CT-ND
RFB2: Res; 0201; RATING *; MANUFACTURER PART NUMBER *; DIGI-KEY PART NUMBER 311-20KNCT-ND
RFB3: Res; 0201; RATING *; MANUFACTURER PART NUMBER *; DIGI-KEY PART NUMBER YAG2785CT-ND
RFB4, RFB6, RFB10: Res; 0201; RATING *; MANUFACTURER PART NUMBER *; DIGI-KEY PART NUMBER YAG2449CT-ND
RFB5, RFB8: Res; 0201; RATING *; MANUFACTURER PART NUMBER *; DIGI-KEY PART NUMBER P122964CT-ND
RFB7: Res; 0201; RATING *; MANUFACTURER PART NUMBER *; DIGI-KEY PART NUMBER YAG2585CT-ND
RFB9: Res; 0201; RATING *; MANUFACTURER PART NUMBER *; DIGI-KEY PART NUMBER YAG2733CT-ND
V1: SC195ULTRT; QFN40P150X150X60-8N-D; MPN SC195ULTRT; DIGI-KEY PART NUMBER SC195ULCT-ND
V2, V3, V5, V6: TPS62240DRVR; SON65P200X200X80-7N; MOUSER PART NUMBER 595-TPS62080ADSGT
V4: TPS62080ADSGR; SON50P200X200X80-9N; MOUSER PART NUMBER 595-TPS62080ADSGT
V7: TPS72718DSER; SON50P150X150X80-6N
VBat: Header 2; HDR1X2; MPN 5-146256-1; DIGI-KEY PART NUMBER A121368-ND

Connections:
D2_CTL1: V1.2 (CTL1)
D2_CTL2: V1.1 (CTL2)
D2_CTL3: V1.8 (CTL3)
unnamed: C21.2, C55.2, J1P8.1, L15.1, RFB5.2
unnamed: C50.2, V2.4 (EN), V2.5 (VIN)
unnamed: C51.2, C56.2, J3P0.1, L16.1, RFB3.2
unnamed: C52.2, V3.5 (VIN)
unnamed: C53.2, V4.1 (EN), V4.8 (VIN)
unnamed: C54.2, J4P0.2, L17.2, R30.2, RFB1.1, V4.5 (VOS)
unnamed: C55.1, RFB5.1, RFB6.2, V2.3 (FB)
unnamed: C56.1, RFB3.1, RFB4.2, V3.3 (FB)
unnamed: C78.2, V1.7 (IN)
unnamed: C79.2, J2P4.1, L14.2, V1.4 (OUT)
unnamed: C94.2, C95.2, L12.1, RFB7.2
unnamed: C95.1, RFB7.1, RFB8.2, V5.3 (FB)
unnamed: C98.2, V5.5 (VIN)
unnamed: C124.1, RFB9.1, RFB10.2, V6.3 (FB)
unnamed: C99.2, C124.2, L20.1, RFB9.2
unnamed: C125.2, V6.5 (VIN)
unnamed: C127.2, V7.4 (EN), V7.6 (IN)
unnamed: C128.2, V7.1 (OUT)
unnamed: L12.2, V5.1 (SW)
unnamed: L14.1, V1.6 (LX)
unnamed: L15.2, V2.1 (SW)
unnamed: L16.2, V3.1 (SW)
unnamed: L17.1, V4.7 (SW)
unnamed: L20.2, V6.1 (SW)
unnamed: R30.1, V4.6 (PG)
unnamed: RFB1.2, RFB2.2, V4.4 (FB)
unnamed: RFB2.1, V4.2 (GND), V4.3 (MODE)
V_3P0_EN: V3.4 (EN)
V_FPGA_EN: V5.4 (EN), V6.4 (EN)

Notes on the sheet:
Sheet:
${LAB}
Date:
Title
${CURRENT_DATE}
${TITLE}
${SHEETNAME}
Power_Input
${REVISION}
HARNESS: D2_PWR_CTRL
HARNESS: REG_Ctrl
Revision:
