uw-x/tinysdr/hardware/pcb-tinysdr/tinysdr_RF.kicad_sch

## KiCad design hardware/pcb-tinysdr/tinysdr_RF.kicad_sch (2022-02-07)

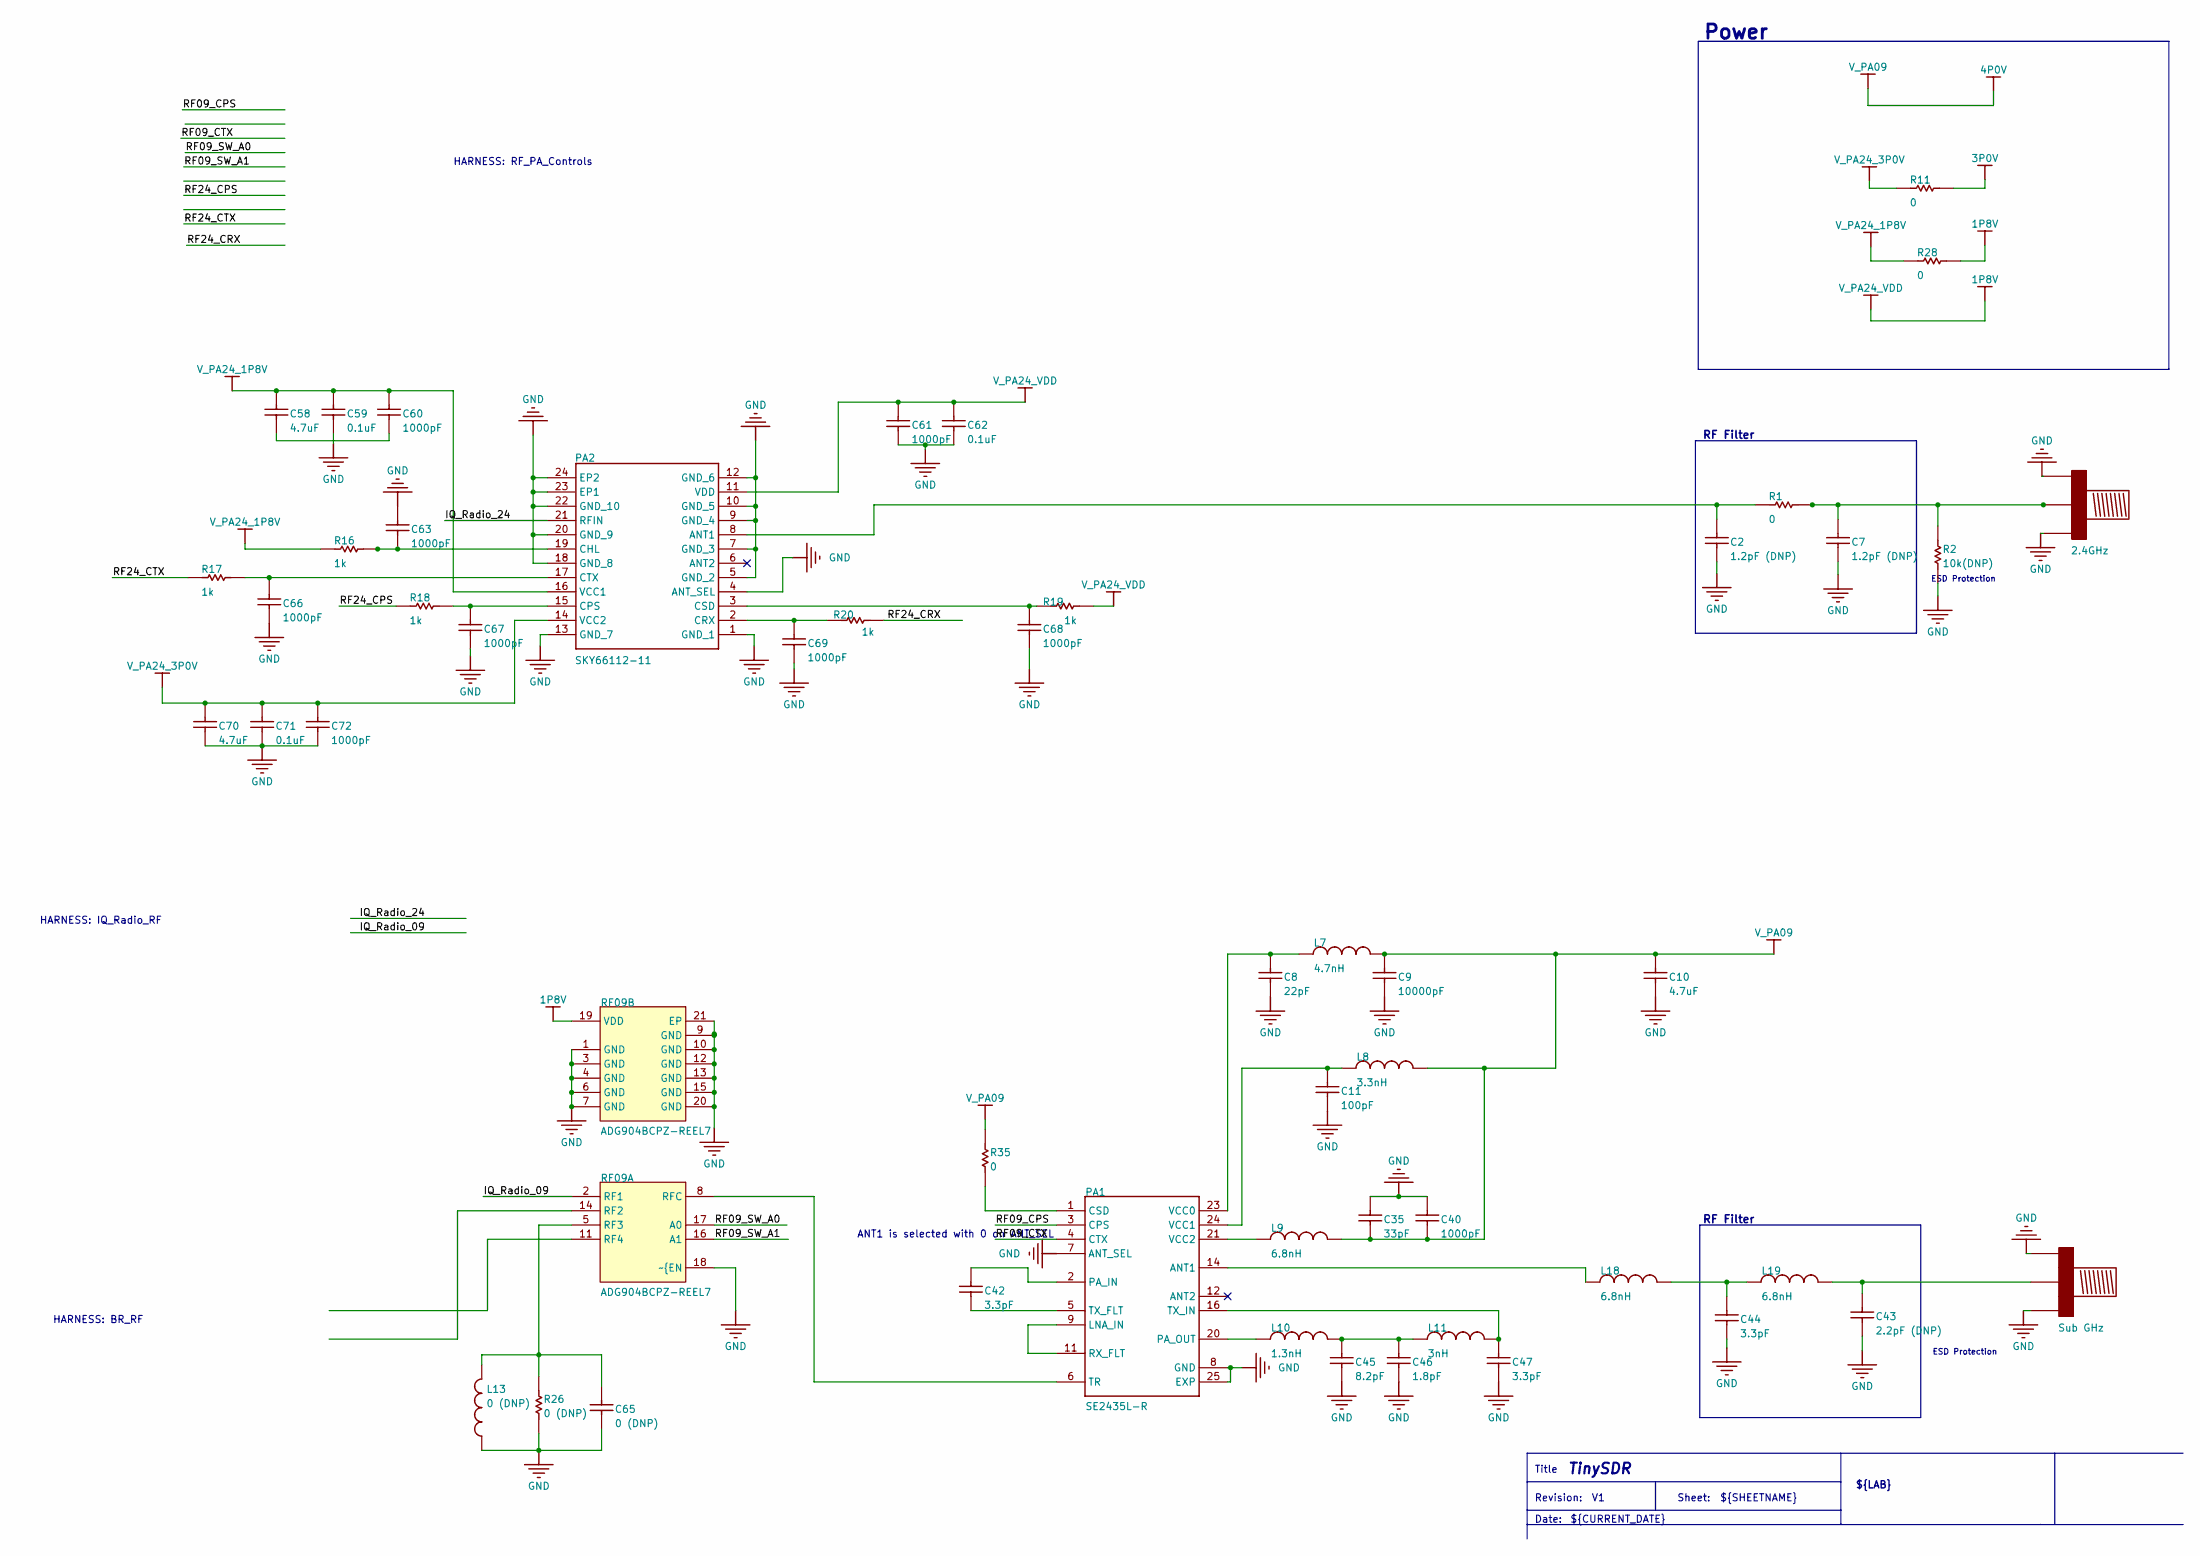
[picture p41: schematic tinysdr_RF.kicad_sch]

Parts:
2.4GHz: SMA - Edge; SMA - Edge - Narrow; MPN CONSMA003.062; DIGI-KEY PART NUMBER CONSMA003.062-ND
C2, C7, C43: Cap; 0201; RATING *; MANUFACTURER PART NUMBER *; DIGI-KEY PART NUMBER *
C8: Cap; 0201; RATING *; MANUFACTURER PART NUMBER *; DIGI-KEY PART NUMBER 490-6123-1-ND
C9: Cap; 0201; RATING *; MANUFACTURER PART NUMBER *; DIGI-KEY PART NUMBER 490-7194-1-ND
C10, C58, C70: Cap; 0201; RATING *; MANUFACTURER PART NUMBER *; DIGI-KEY PART NUMBER 490-13230-1-ND
C11: Cap; 0201; RATING *; MANUFACTURER PART NUMBER *; DIGI-KEY PART NUMBER 490-6113-1-ND
C35: Cap; 0201; RATING *; MANUFACTURER PART NUMBER *; DIGI-KEY PART NUMBER 490-6126-1-ND
C40, C60, C61, C63, C66, C67, C68, C69, C72: Cap; 0201; RATING *; MANUFACTURER PART NUMBER *; DIGI-KEY PART NUMBER 490-3184-1-ND
C42, C44, C47: Cap; 0201; RATING *; MANUFACTURER PART NUMBER *; DIGI-KEY PART NUMBER 490-6128-1-ND
C45: Cap; 0201; RATING *; MANUFACTURER PART NUMBER *; DIGI-KEY PART NUMBER 490-6133-1-ND
C46: Cap; 0201; RATING *; MANUFACTURER PART NUMBER *; DIGI-KEY PART NUMBER 490-11314-1-ND
C59, C62, C71: Cap; 0201; RATING *; MANUFACTURER PART NUMBER *; DIGI-KEY PART NUMBER 490-10387-1-ND
C65: Cap; 0201; RATING *; MANUFACTURER PART NUMBER *
L7: Ind; _work_pcb_xsdr_v2_Libraries_WREL_AD10_Ben.PcbLib_0201; RATING *; MANUFACTURER PART NUMBER *; DIGI-KEY PART NUMBER 490-7788-1-ND
L8: Ind; _work_pcb_xsdr_v2_Libraries_WREL_AD10_Ben.PcbLib_0201; RATING *; MANUFACTURER PART NUMBER *; DIGI-KEY PART NUMBER 490-6728-1-ND
L9, L18, L19: Ind; _work_pcb_xsdr_v2_Libraries_WREL_AD10_Ben.PcbLib_0201; RATING *; MANUFACTURER PART NUMBER *; DIGI-KEY PART NUMBER 490-5564-1-ND
L10: Ind; _work_pcb_xsdr_v2_Libraries_WREL_AD10_Ben.PcbLib_0201; RATING *; MANUFACTURER PART NUMBER *; DIGI-KEY PART NUMBER 490-6717-1-ND
L11: Ind; _work_pcb_xsdr_v2_Libraries_WREL_AD10_Ben.PcbLib_0201; RATING *; MANUFACTURER PART NUMBER *; DIGI-KEY PART NUMBER 490-6727-1-ND
L13: Ind; _work_pcb_xsdr_v2_Libraries_WREL_AD10_Ben.PcbLib_0201; RATING *; MANUFACTURER PART NUMBER *
PA1: SE2435L-R; QFN50P400X400X90-25N; MPN SE2435L-R; DIGI-KEY PART NUMBER 863-1349-1-ND
PA2: SKY66112-11; SKY6611211; MANUFACTURER_PART_NUMBER SKY66112-11; MOUSER PART NUMBER 873-SKY66112-11
R1: Res; 0201; RATING *; MANUFACTURER PART NUMBER *; DIGI-KEY PART NUMBER P15979CT-ND
R2, R26: Res; 0201; RATING *; MANUFACTURER PART NUMBER *
R11, R28, R35: Res; 0402; RATING *; MANUFACTURER PART NUMBER *; DIGI-KEY PART NUMBER 541-0.0YBCT-ND
R16, R17, R18, R19, R20: Res; 0201; RATING *; MANUFACTURER PART NUMBER *; DIGI-KEY PART NUMBER 311-1KMCT-ND
RF09: ADG904BCPZ-REEL7; ADI-CP-20-6_L; PARTNUMBER ADG904BCPZ-REEL7; DIGI-KEY PART NUMBER ADG904BCPZ-REEL7CT-ND
Sub GHz: SMA - Edge; SMA - Edge - Narrow; MPN CONSMA003.062; DIGI-KEY PART NUMBER CONSMA003.062-ND

Connections:
IQ_Radio_09: RF09.2 (RF1)
IQ_Radio_24: PA2.21 (RFIN)
unnamed: 2.4GHz.2, C7.2, R1.1, R2.2
unnamed: C2.2, PA2.8 (ANT1), R1.2
unnamed: C8.1, L7.1, PA1.23 (VCC0)
unnamed: C9.1, C10.1, C35.1, C40.1, L7.2, L8.2, L9.2
unnamed: C11.1, L8.1, PA1.24 (VCC1)
unnamed: C35.2, C40.2
unnamed: C42.1, PA1.5 (TX_FLT)
unnamed: C42.2, PA1.2 (PA_IN)
unnamed: C43.2, L19.2, Sub GHz.2
unnamed: C44.2, L18.2, L19.1
unnamed: C45.1, C46.1, L10.2, L11.1
unnamed: C47.1, L11.2, PA1.16 (TX_IN)
unnamed: C58.1, C60.1
unnamed: C58.2, C59.2, C60.2, PA2.16 (VCC1)
unnamed: C61.1, C62.1
unnamed: C61.2, C62.2, PA2.11 (VDD)
unnamed: C63.2, PA2.19 (CHL), R16.1
unnamed: C65.1, L13.1, R26.1
unnamed: C65.2, L13.2, R26.2, RF09.5 (RF3)
unnamed: C66.2, PA2.17 (CTX), R17.1
unnamed: C67.1, PA2.15 (CPS), R18.1
unnamed: C68.2, PA2.3 (CSD), R19.1
unnamed: C69.2, PA2.2 (CRX), R20.1
unnamed: C70.1, C71.1, C72.1
unnamed: C70.2, C71.2, C72.2, PA2.14 (VCC2)
unnamed: L9.1, PA1.21 (VCC2)
unnamed: L10.1, PA1.20 (PA_OUT)
unnamed: L18.1, PA1.14 (ANT1)
unnamed: PA1.1 (CSD), R35.2
unnamed: PA1.6 (TR), RF09.8 (RFC)
unnamed: PA1.9 (LNA_IN), PA1.11 (RX_FLT)
unnamed: PA1.8 (GND), PA1.25 (EXP)
unnamed: PA2.5 (GND_2), PA2.7 (GND_3), PA2.9 (GND_4), PA2.10 (GND_5), PA2.12 (GND_6)
unnamed: PA2.18 (GND_8), PA2.20 (GND_9), PA2.22 (GND_10), PA2.23 (EP1), PA2.24 (EP2)
unnamed: RF09.1 (GND), RF09.3 (GND), RF09.4 (GND), RF09.6 (GND), RF09.7 (GND)
unnamed: RF09.9 (GND), RF09.10 (GND), RF09.12 (GND), RF09.13 (GND), RF09.15 (GND), RF09.20 (GND), RF09.21 (EP)
RF09_CPS: PA1.3 (CPS)
RF09_CTX: PA1.4 (CTX)
RF09_SW_A0: RF09.17 (A0)
RF09_SW_A1: RF09.16 (A1)
RF24_CPS: R18.2
RF24_CRX: R20.2
RF24_CTX: R17.2

Notes on the sheet:
HARNESS: BR_RF
HARNESS: IQ_Radio_RF
ESD Protection
${REVISION}
Sheet:
HARNESS: RF_PA_Controls
Title
RF Filter
Power
${CURRENT_DATE}
${TITLE}
Date:
${LAB}
Revision:
${SHEETNAME}
ANT1 is selected with 0 on ANT_SEL
