uw-x/tinysdr/firmware/main.c

#include <at86rf215/at86rf215.h>
#include "system/libraries/board.h"
#include <stdio.h>
#include "msp.h"
#include <stdbool.h>
#include <driverlib.h>
#include "settings.h"
#include "system/libraries/clock.h"
//#include "testmini.h"
#include <fpga.h>
#include <ble.h>
#include "system/libraries/i2c.h"
#include <mcp9808/mcp9808.h>
#include <utils/utils.h>
#include <app/task.h>



/**#############################Variables#############################**/
Board_t TinySDR;
MCU_States_t MCU_State = MCU_STATE_INIT;
#define modem   0

/**#############################Test#############################**/
#pragma DATA_SECTION(flash,"flashBuff");
const uint8_t flash [99962] = {
0xFF,0xFF,0xFF,0xFF,0xFF,0xFF,0xFF,0xFF,0xFF,0xFF,0xFF,0xFF,0xFF,0xFF,0xFF,0xFF,0xFF,0xFF,0xFF,0xFF,0xFF,0xFF,0xFF,0xFF,0xFF,0xFF,0xFF,0xFF,0xFF,0xFF,0xFF,0xFF,0xFF,0xFF,0xFF,0xFF,0xFF,0xFF,0xFF,0xFF,0xFF,0xFF,0xFF,0xFF,0xFF,0xFF,0xFF,0xFF,0xFF,0xFF,0xFF,0xFF,0xFF,0xFF,0xFF,0xFF,0xFF,0xFF,0xFF,0xFF,0xFF,0xFF,0xFF,0xFF,0xFF,0xFF,0xFF,0xFF,0xFF,0xFF,0xFF,0xFF,0xFF,0xFF,0xFF,0xFF,0xFF,0xFF,0xFF,0xFF,0xFF,0xFF,0xFF,0xFF,0xFF,0xFF,0xFF,0xFF,0xFF,0xFF,0xFF,0xFF,0xFF,0xFF,0xFF,0xFF,0xFF,0xFF,0xFF,0xFF,0xFF,0xFF,0xFF,0xFF,0xFF,0xFF,0xFF,0xFF,0xFF,0xFF,0xFF,0xFF,0xFF,0xFF,0xFF,0xFF,0xFF,0xFF,0xFF,0xFF,0xFF,0xFF,0xFF,0xFF,0xFF,0xFF,0xFF,0xFF,0xFF,0xFF,0xFF,0xFF,0xFF,0xFF,0xFF,0xFF,0xFF,0xFF,0xFF,0xFF,0xFF,0xFF,0xFF,0xFF,0xFF,0xFF,0xFF,0xFF,0xFF,0xFF,0xFF,0xFF,0xFF,0xFF,0xFF,0xFF,0xFF,0xFF,0xFF,0xFF,0xFF,0xFF,0xFF,0xFF,0xFF,0xFF,0xFF,0xFF,0xFF,0xFF,0xFF,0xFF,0xFF,0xFF,0xFF,0xFF,0xFF,0xFF,0xFF,0xFF,0xFF,0xFF,0xFF,0xFF,0xFF,0xFF,0xFF,0xFF,0xFF,0xFF,0xFF,0xFF,0xFF,0xFF,0xFF,0xFF,0xFF,0xFF,0xFF,0xFF,0xFF,0xFF,0xFF,0xFF,0xFF,0xFF,0xFF,0xFF,0xFF,0xFF,0xFF,0xFF,0xFF,0xFF,0xFF,0xFF,0xFF,0xFF,0xFF,0xFF,0xFF,0xFF,0xFF,0xFF,0xFF,0xFF,0xFF,0xFF,0xFF,0xFF,0xFF,0xFF,0xFF,0xFF,0xFF,0xFF,0xFF,0xFF,0xFF,0xFF,0xFF,0xFF,0xFF,0xFF,0xFF,0xFF,0xFF,0xFF,0xFF,0xFF,0xFF,0xFF,0xFF,0xFF,0xFF,0xFF,0xFF,0xFF,0xFF,0xFF,0xFF,0xFF,0xFF,0xFF,0xFF,0xFF,0xFF,0xFF,0xFF,0xFF,0xFF,0xFF,0xFF,0xFF,0xFF,0xFF,0xFF,0xFF,0xFF,0xFF,0xFF,0xFF,0xFF,0xFF,0xFF,0xFF,0xFF,0xFF,0xFF,0xFF,0xFF,0xFF,0xFF,0xFF,0xFF,0xFF,0xFF,0xFF,0xFF,0xFF,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
0x00,0x00,0x00,0x00,0x00,0x00,0x00,0x00,0xcc,0xe8,0xff,0x00,0x00,0x00,0x00,0x00,0x00,0x00,0x00,0x00,0x00,0xcc,0xe8,0xff,0x00,0x00,0x00,0x00,0x00,0x00,0x00,0x00,0x00,0x00,0xcc,0xe8,0xff,0x00,0x00,0x00,0x00,0x00,0x00,0x00,0x00,0x00,0x00,0xcc,0xe8,0xff,0x00,0x00,0x00,0x00,0x00,0x00,0x00,0x00,0x00,0x00,0xcc,0xe
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
int main(void)
{
//  task_ble();
//##################### Initialization ########################################
    ////Stop watchdog timer
    MAP_WDT_A_holdTimer();


//##################### Task ########################################
//    task_ext_flash();
//    task_fpga_lora_tx();
//    task_power_measure();
//    task_lora_test();
    task_fpga();




//#if modem == 0
//    AT86RF215SetModem(MODEM_09);
//    setSwitchMode(AT86RF215.RF_Settings.Modem);
//    Frequency = 915000000;
//    setPA(PA_900, PA_TX_Bypass);
////    RX_Frequency = 884203125;
//#else
//    AT86RF215SetModem(MODEM_24);
//    setSwitchMode(AT86RF215.RF_Settings.Modem);
////    Frequency = 2478000000 + 23500;
//    Frequency = 2402000000 + 23500;
//    setPA(PA_2400, PA_TX_Bypass);
//#endif



//    At86rf215Radio.Init(&at86rf215RE);
   // GpioWrite(&AT86RF215.LED_D2, true);

//    task_i2c();


//##################### Max Tests ########################################
//     ClockInit();
//     BoardInitMcu();
//     BoardPWRInit();
//     GpioWrite(&TinySDR.LED_D1, true);
//     GpioWrite(&TinySDR.LED_D2, true);
//     while(1)
//      {
//
//      }


//##################### Radio Mode ########################################
//  #if Radio_Mode == Radio_Mode_SingleTone
//      AT86RF215SetCWSingleTone(Frequency);
//  #elif Radio_Mode == Radio_Mode_IQ_TX
//      AT86RF215TxSetIQ(Frequency);
//  #elif Radio_Mode == Radio_Mode_IQ_RX
//      AT86RF215RxSetIQ(RX_Frequency);
//  #elif Radio_Mode == Radio_Mode_BB_PHY_RX
//      AT86RF215RxSetBBFSK(RX_Frequency);
//  #endif


    delay_ms(1);
    #if Radio_Mode == Radio_Mode_SingleTone
        AT86RF215SetState(RF_CMD_TX);
    #elif Radio_Mode == Radio_Mode_IQ_TX
        AT86RF215SetState(RF_CMD_TX);
    #elif Radio_Mode == Radio_Mode_IQ_RX
        AT86RF215SetState(RF_CMD_RX);
    #elif Radio_Mode == Radio_Mode_BB_PHY_RX
        AT86RF215SetState(RF_CMD_RX);
    #endif

    fpgaSetConfig(0);
    //FPGA firmware load
    delay_ms(2000);
    fpgaReset();

}
